kerby2000/PetSafe-PCB/output/measurement_round1-1.png

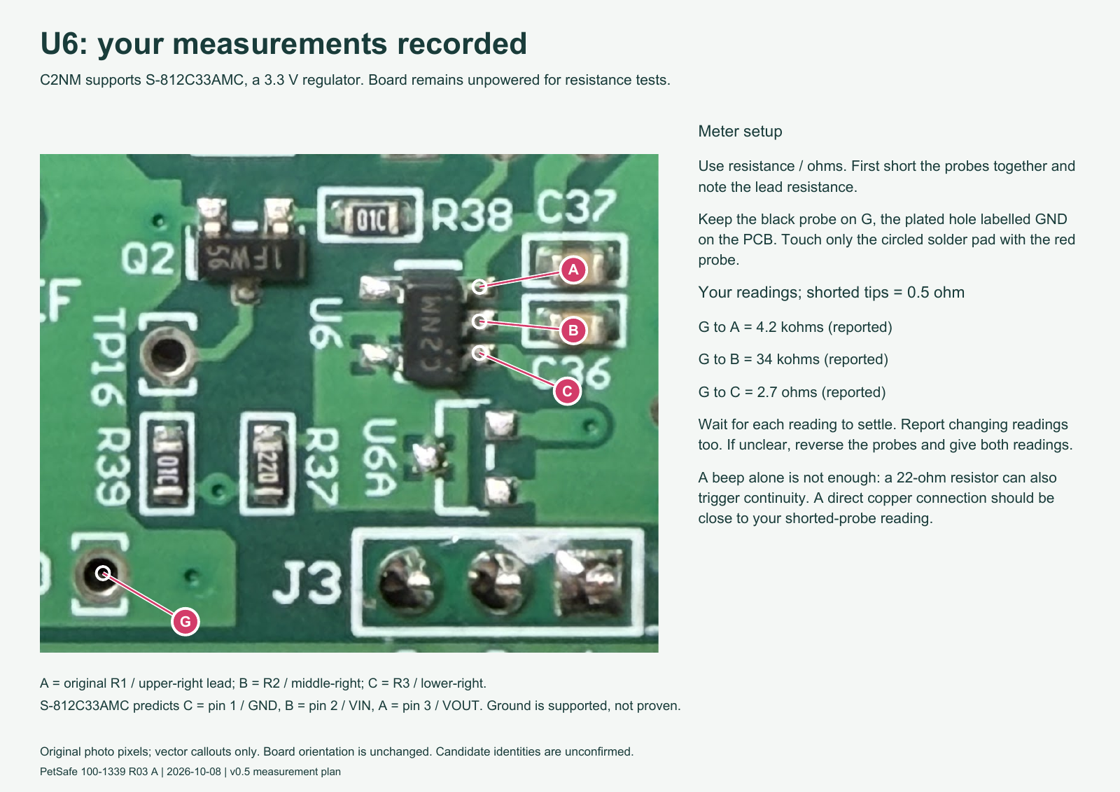
output/measurement_round1-1.png
