kerby2000/PetSafe-PCB/output/D2_D3_location_v1.png

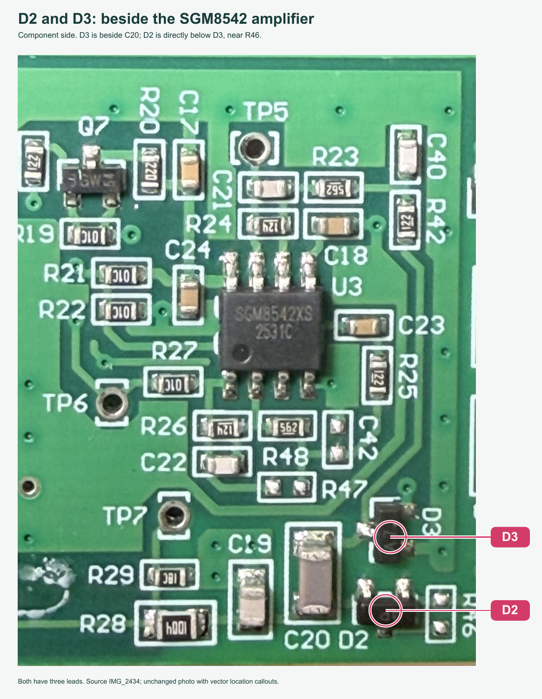
output/D2_D3_location_v1.png
