kerby2000/PetSafe-PCB/output/PetSafe_PIC_GPIO_pin_map.png

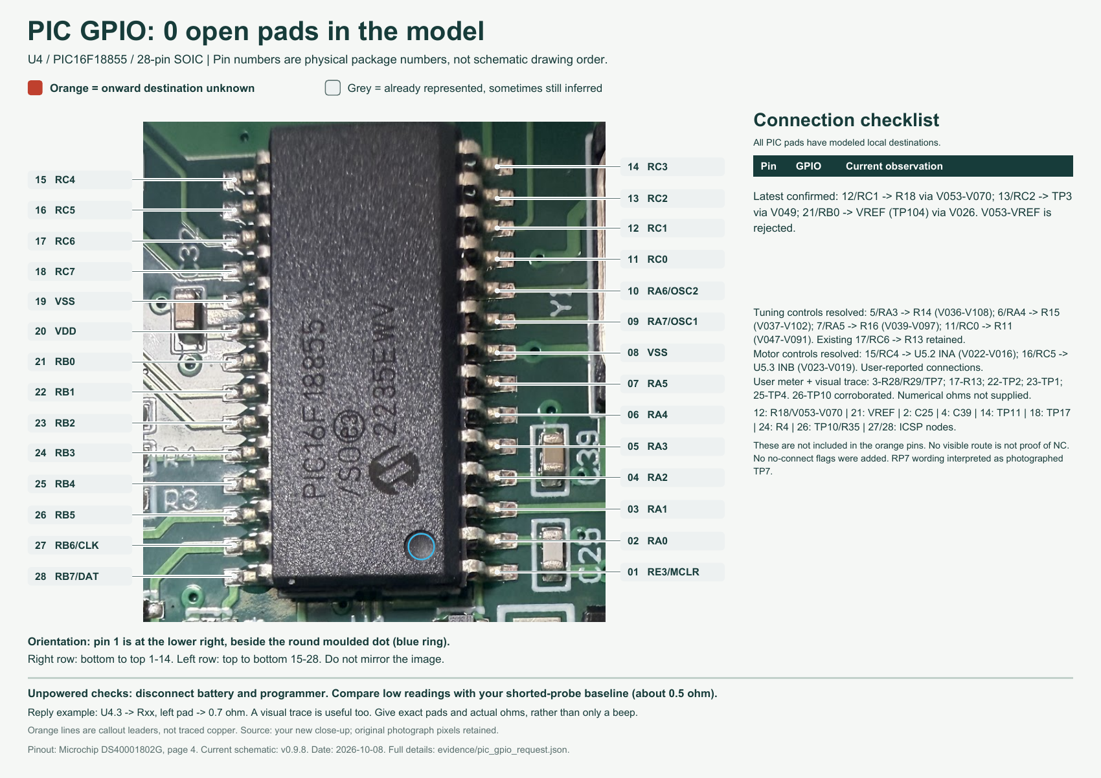
output/PetSafe_PIC_GPIO_pin_map.png
