kerby2000/PetSafe-PCB/output/Q8_C6_followup_with_P.png

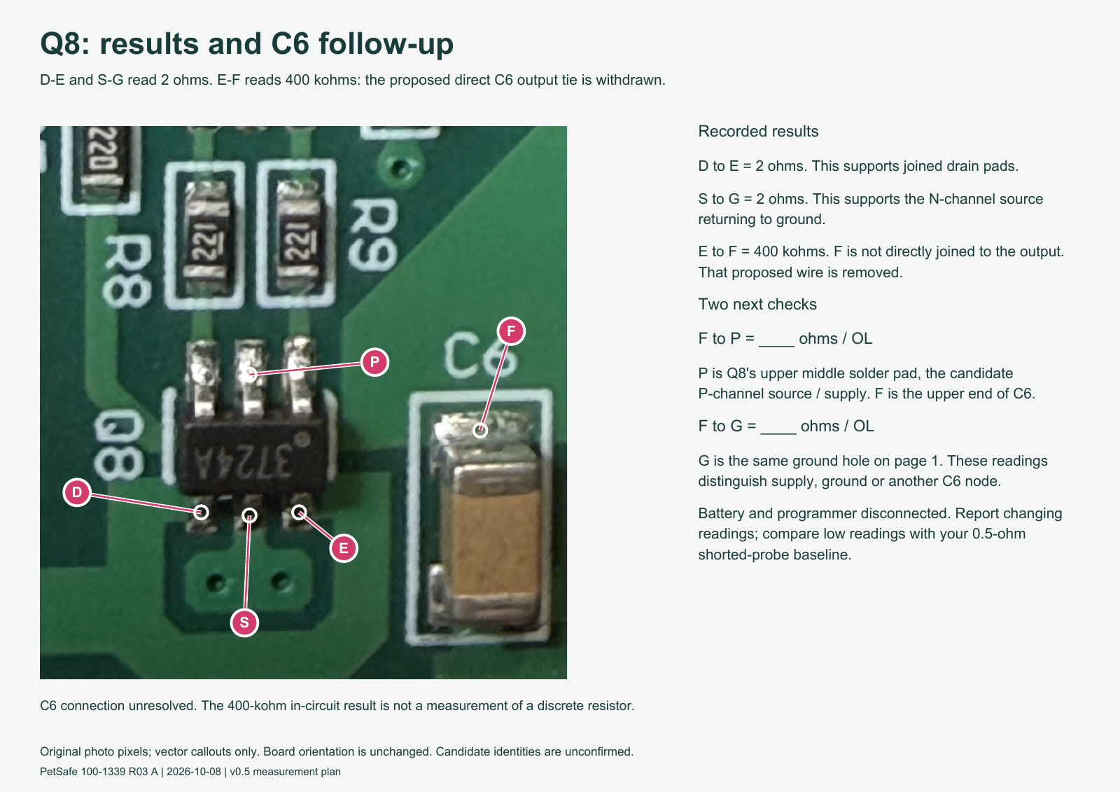
output/Q8_C6_followup_with_P.png
