kerby2000/PetSafe-PCB/output/single_sheet_preview.png

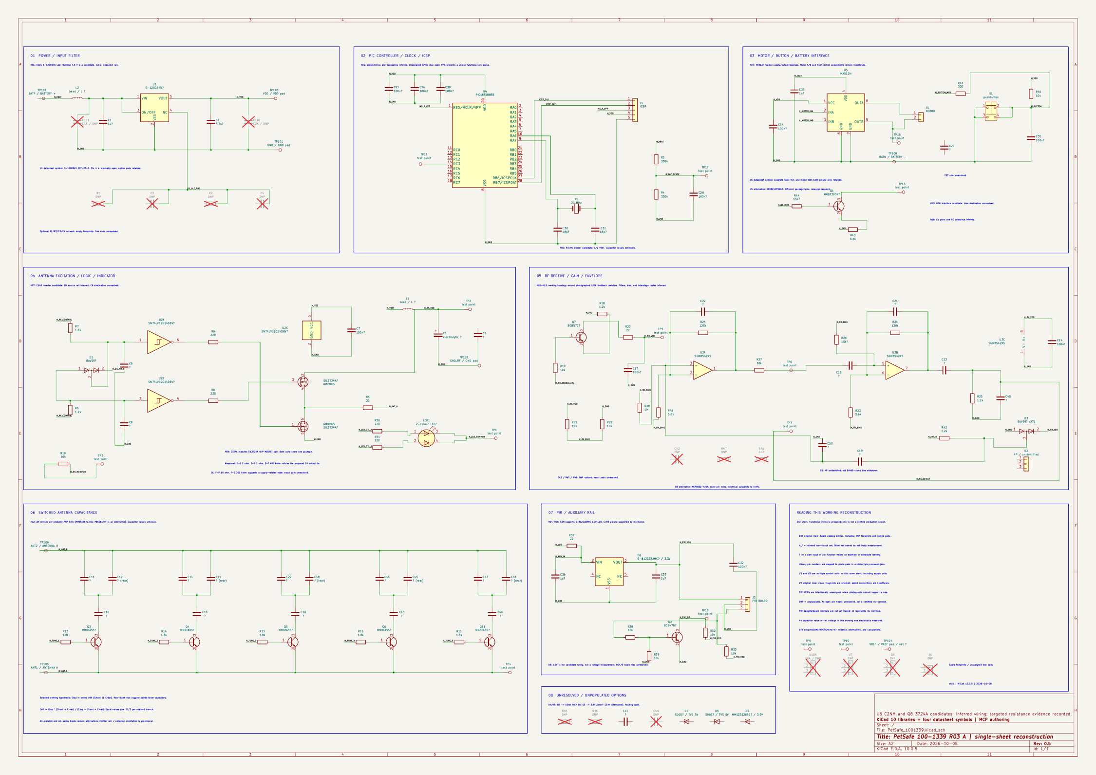
output/single_sheet_preview.png
