kerby2000/PetSafe-PCB/photos/back_mirrored_registered.jpg

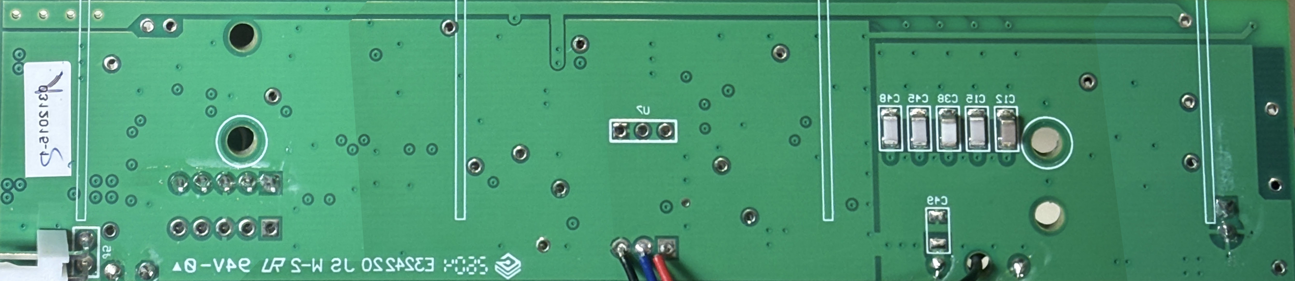
photos/back_mirrored_registered.jpg
