kerby2000/PetSafe-PCB/photos/back_readable.jpg

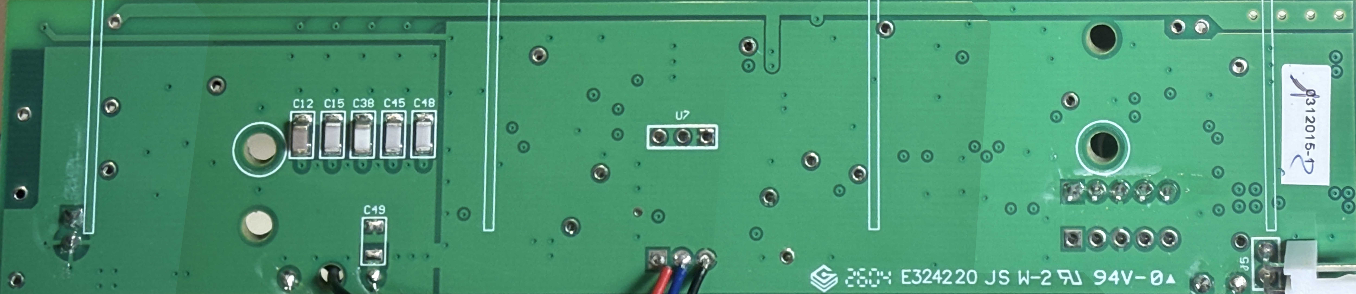
photos/back_readable.jpg
