kerby2000/PetSafe-PCB/photos/back_source_ids_unrectified.png

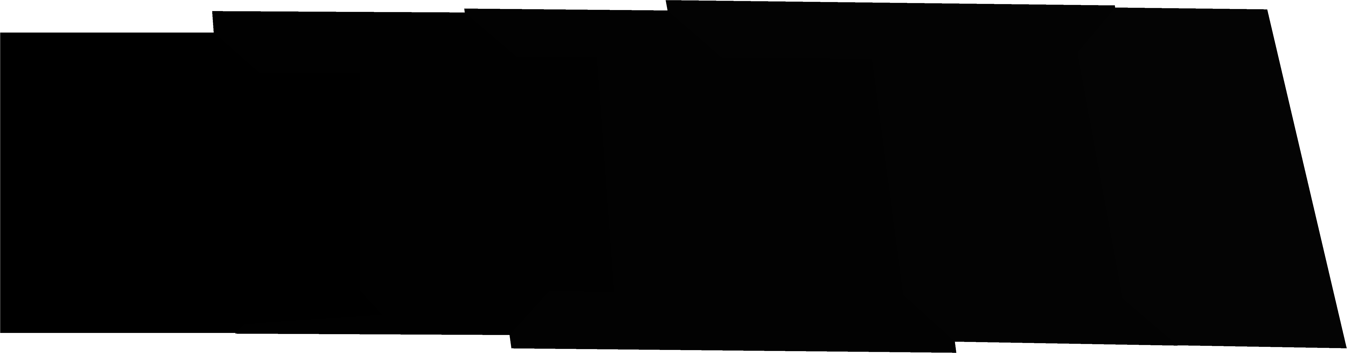
photos/back_source_ids_unrectified.png
