kerby2000/PetSafe-PCB/photos/front_preview.jpg

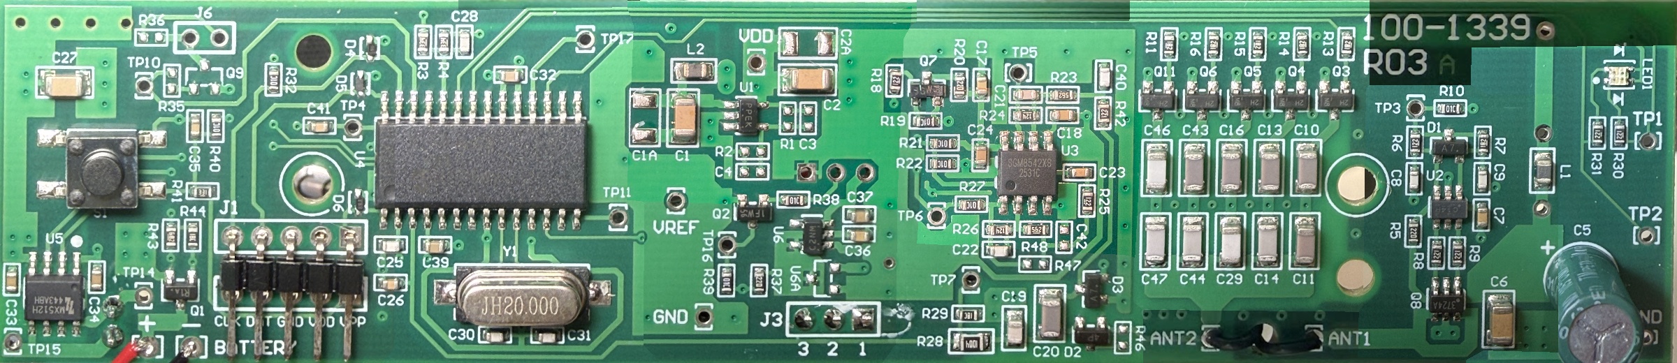
photos/front_preview.jpg
