kerby2000/PetSafe-PCB/photos/investigation/Q8_detail.png

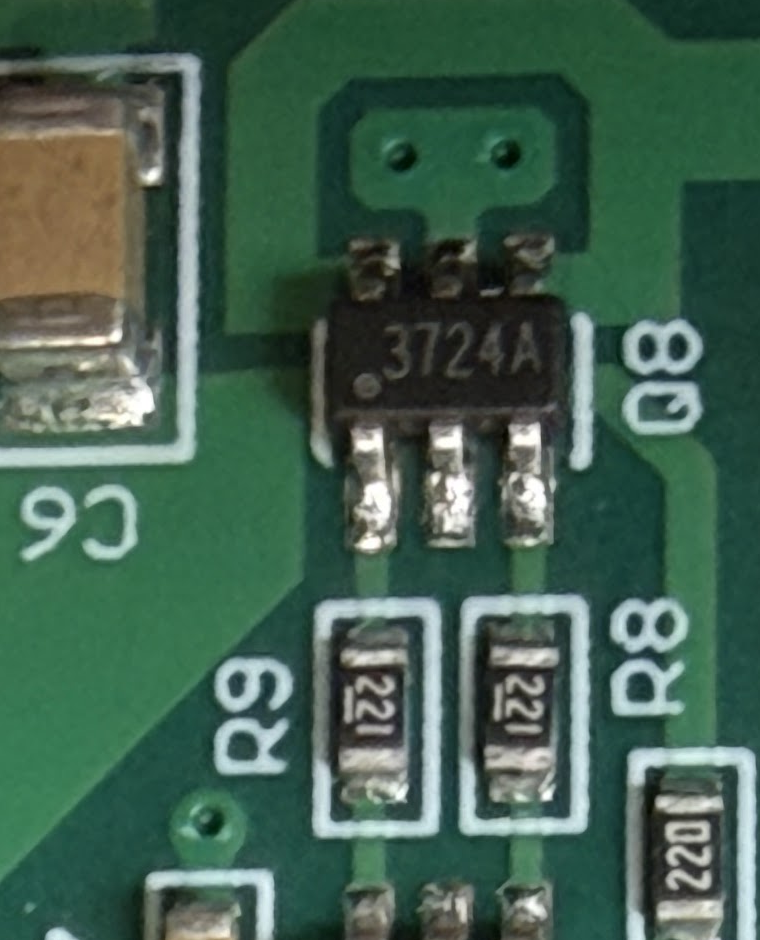
photos/investigation/Q8_detail.png
