kerby2000/PetSafe-PCB/photos/investigation/U6_detail.png

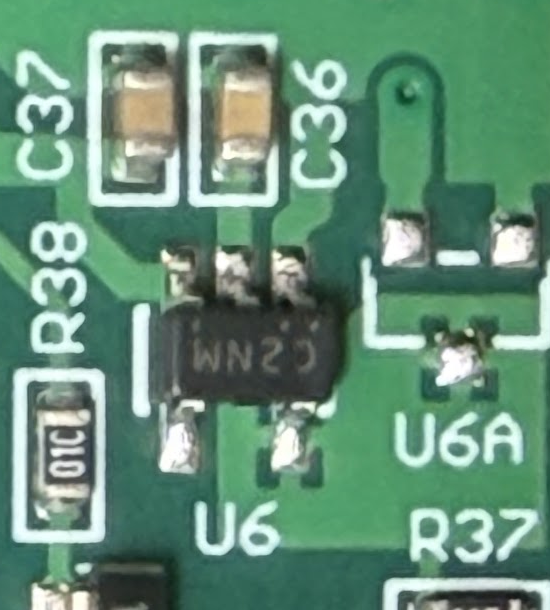
photos/investigation/U6_detail.png
