kerby2000/PetSafe-PCB/photos/originals/IMG_2417.jpg

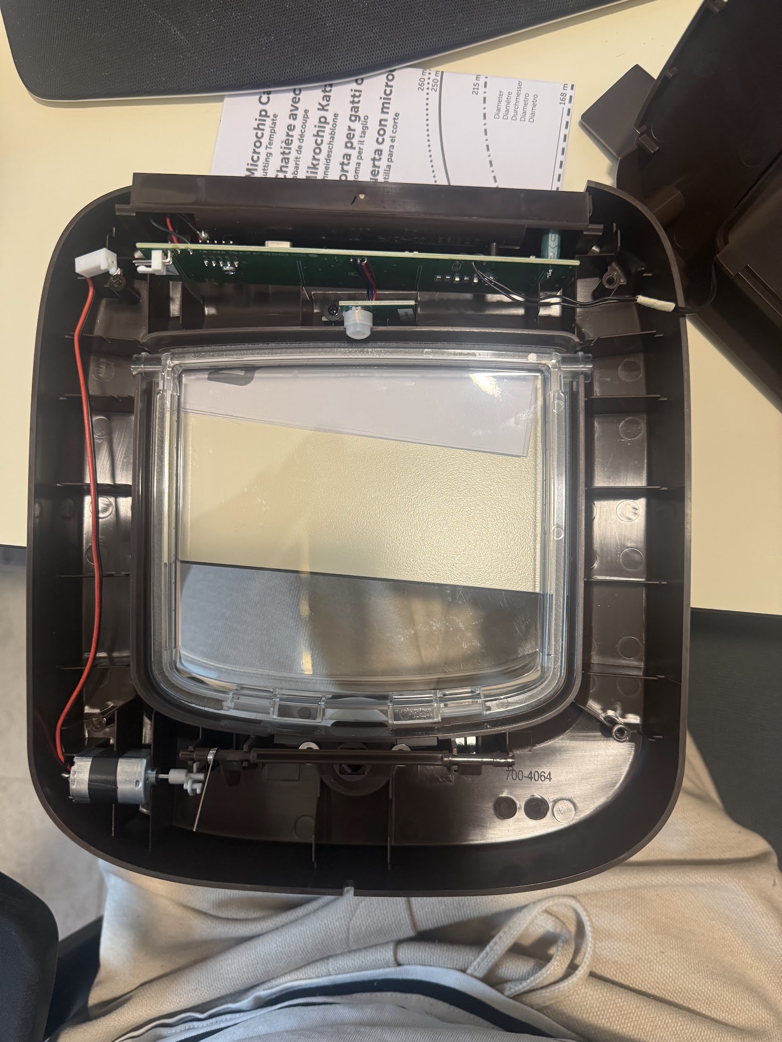
photos/originals/IMG_2417.jpg
