kerby2000/PetSafe-PCB/photos/originals/IMG_2418.jpg

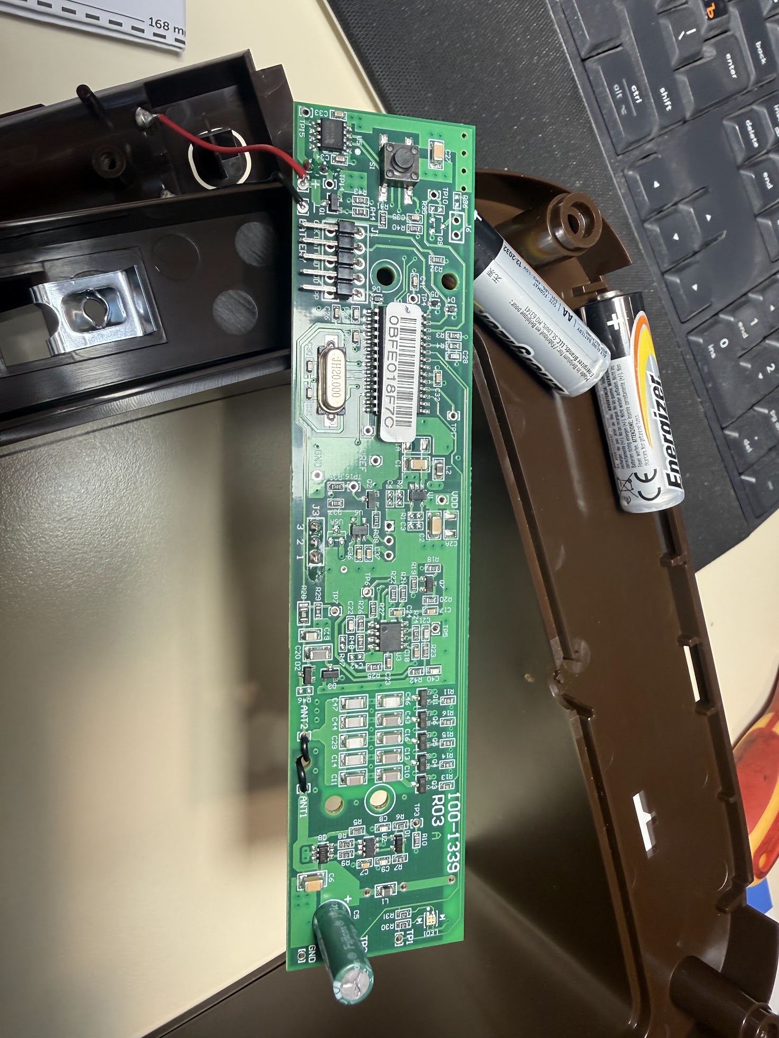
photos/originals/IMG_2418.jpg
