kerby2000/PetSafe-PCB/photos/originals/IMG_2419.jpg

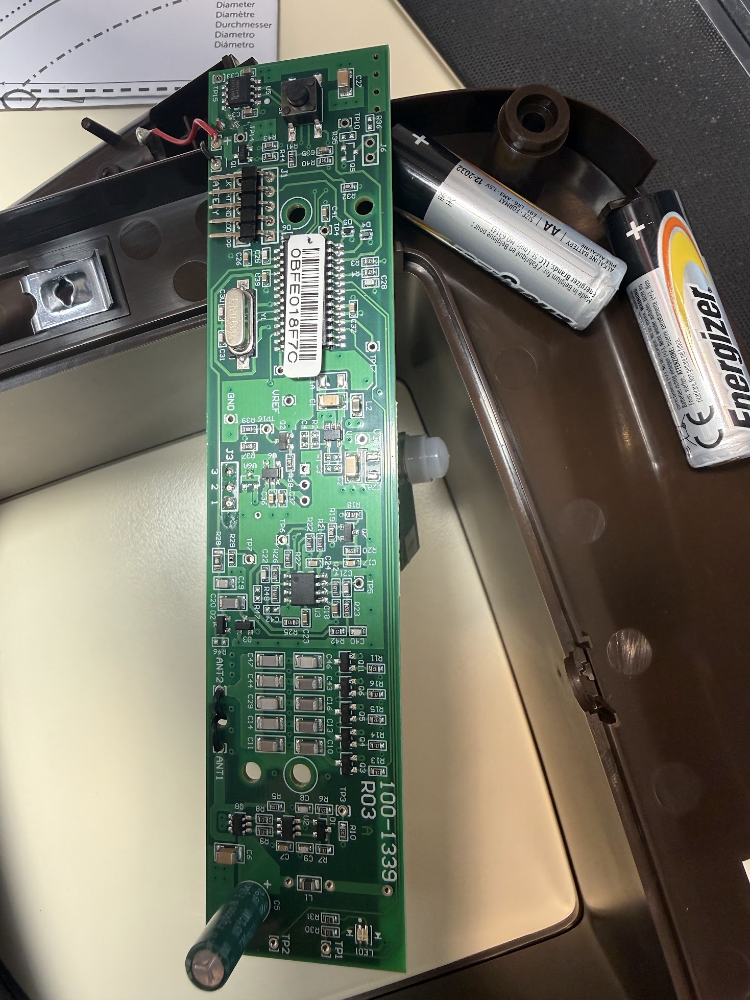
photos/originals/IMG_2419.jpg
