kerby2000/PetSafe-PCB/photos/originals/IMG_2420.jpg

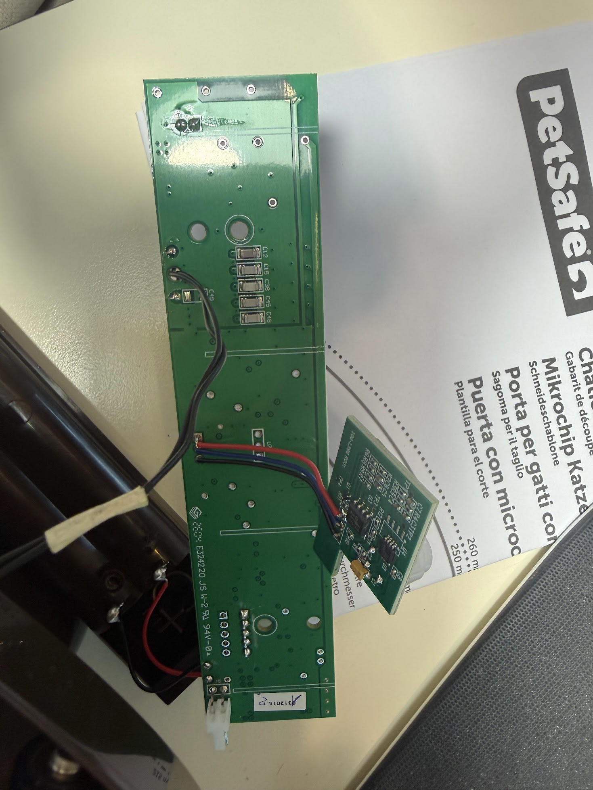
photos/originals/IMG_2420.jpg
