kerby2000/PetSafe-PCB/photos/originals/IMG_2421.jpg

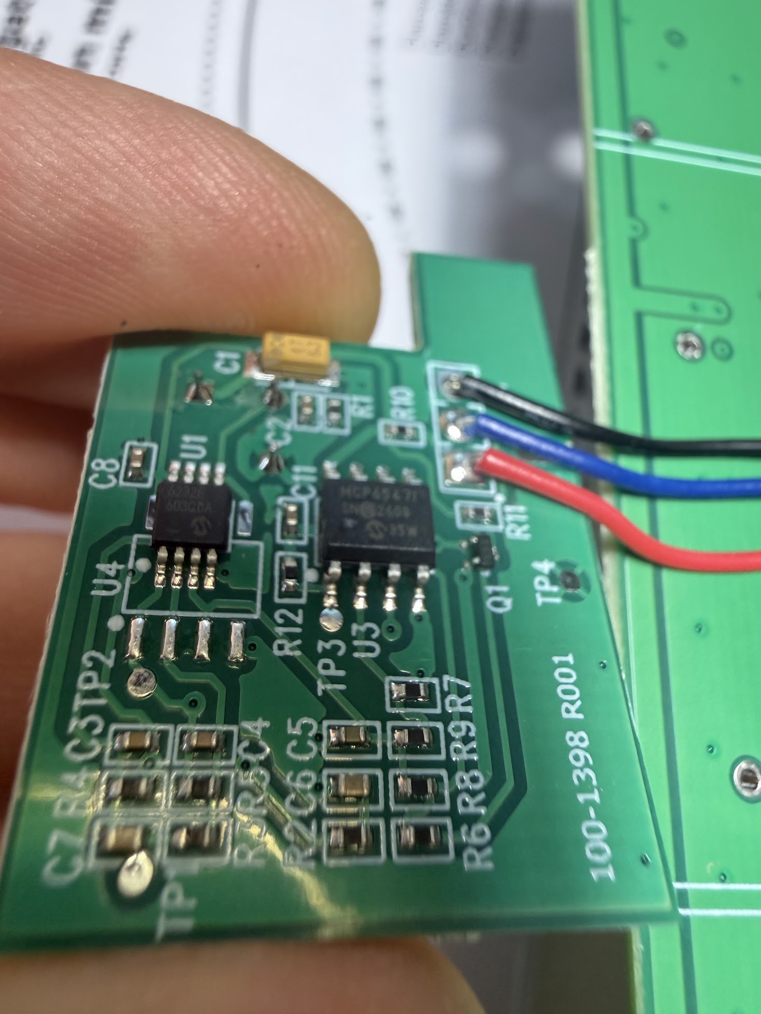
photos/originals/IMG_2421.jpg
