kerby2000/PetSafe-PCB/photos/originals/IMG_2422.jpg

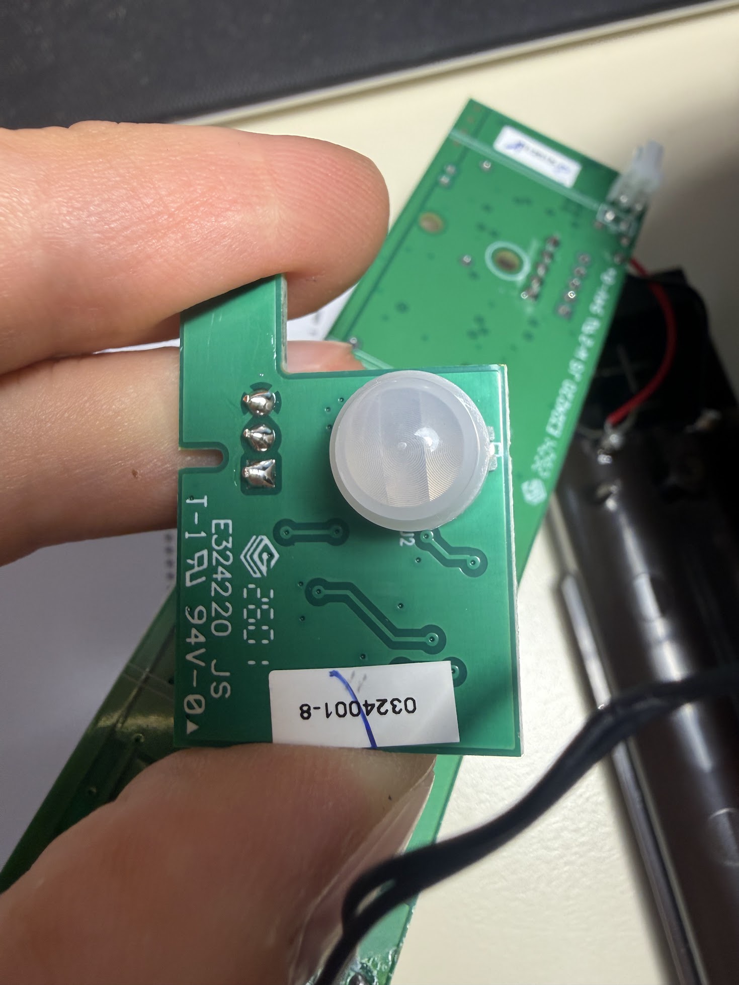
photos/originals/IMG_2422.jpg
