kerby2000/PetSafe-PCB/photos/originals/IMG_2423.jpg

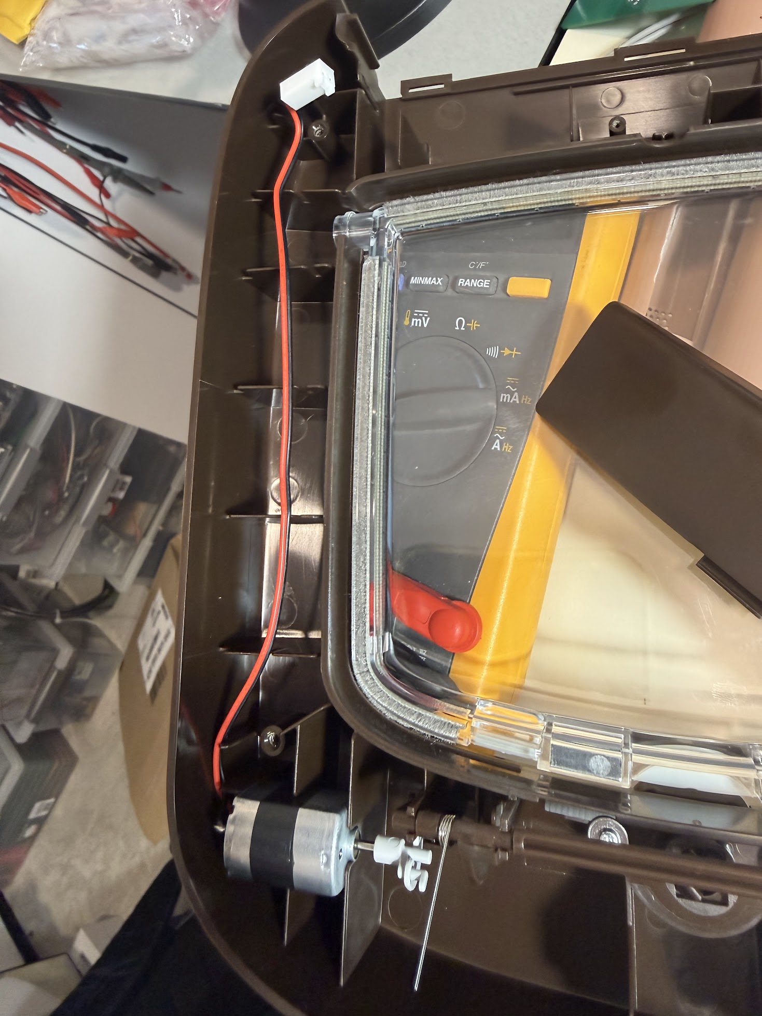
photos/originals/IMG_2423.jpg
