kerby2000/PetSafe-PCB/photos/originals/IMG_2424.jpg

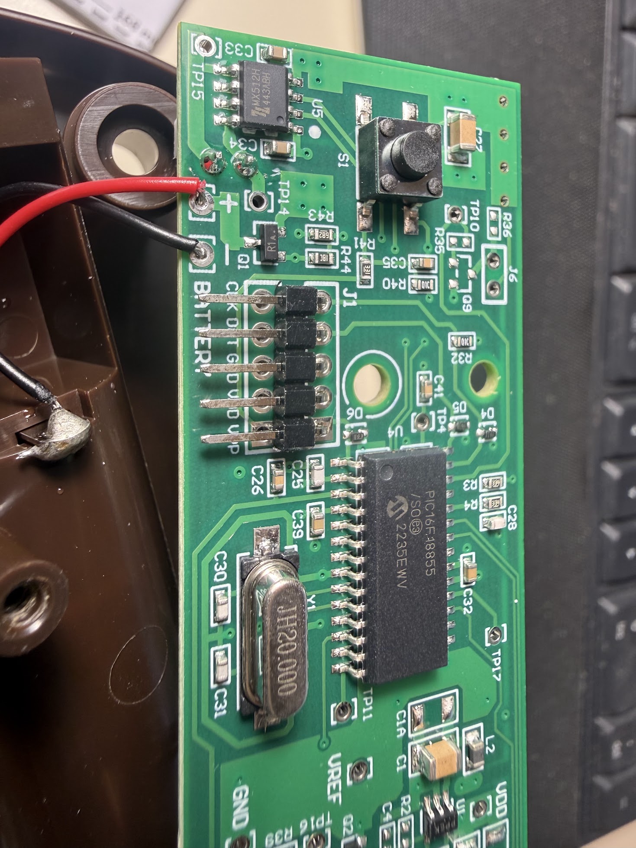
photos/originals/IMG_2424.jpg
