kerby2000/PetSafe-PCB/photos/originals/IMG_2425.jpg

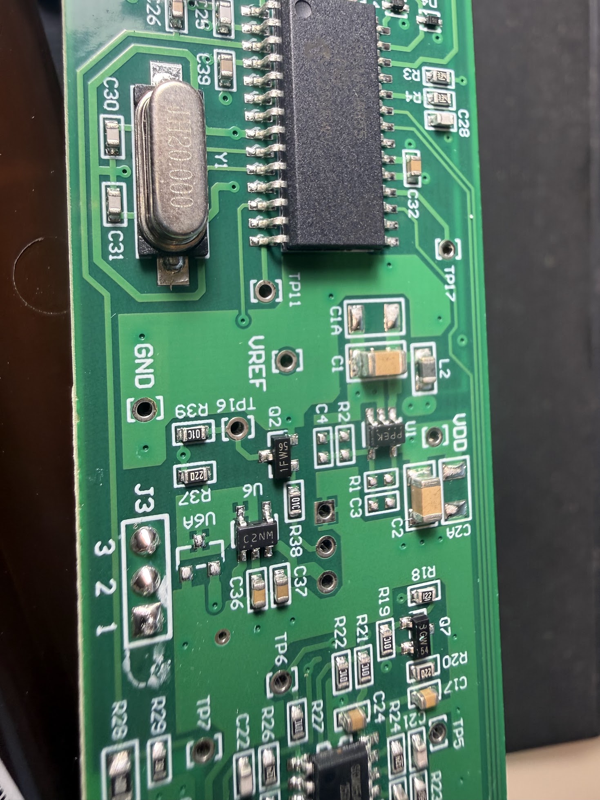
photos/originals/IMG_2425.jpg
