kerby2000/PetSafe-PCB/photos/originals/IMG_2427.jpg

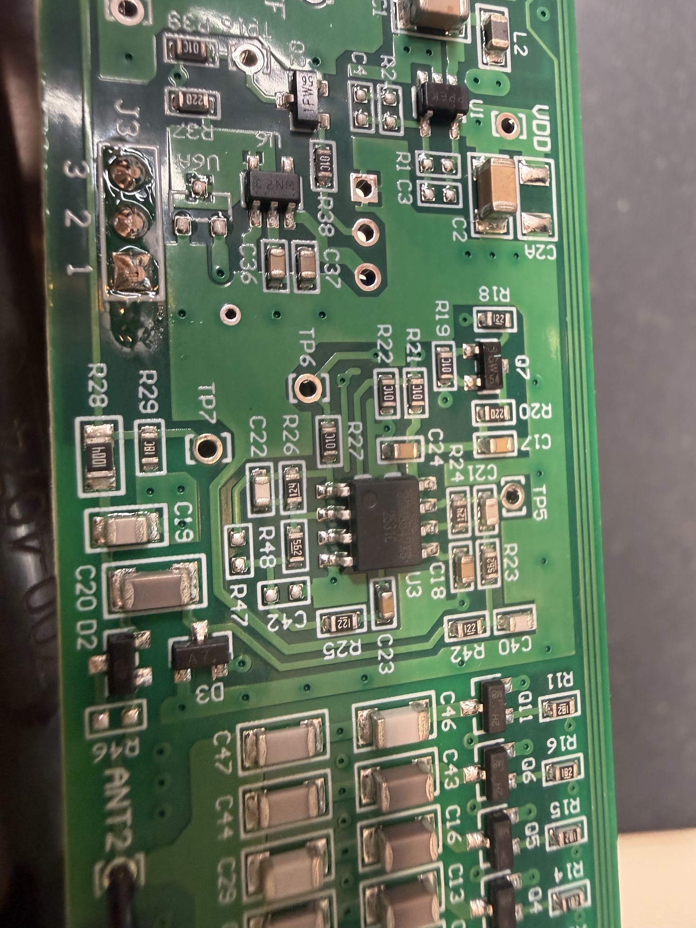
photos/originals/IMG_2427.jpg
