kerby2000/PetSafe-PCB/photos/originals/IMG_2428.jpg

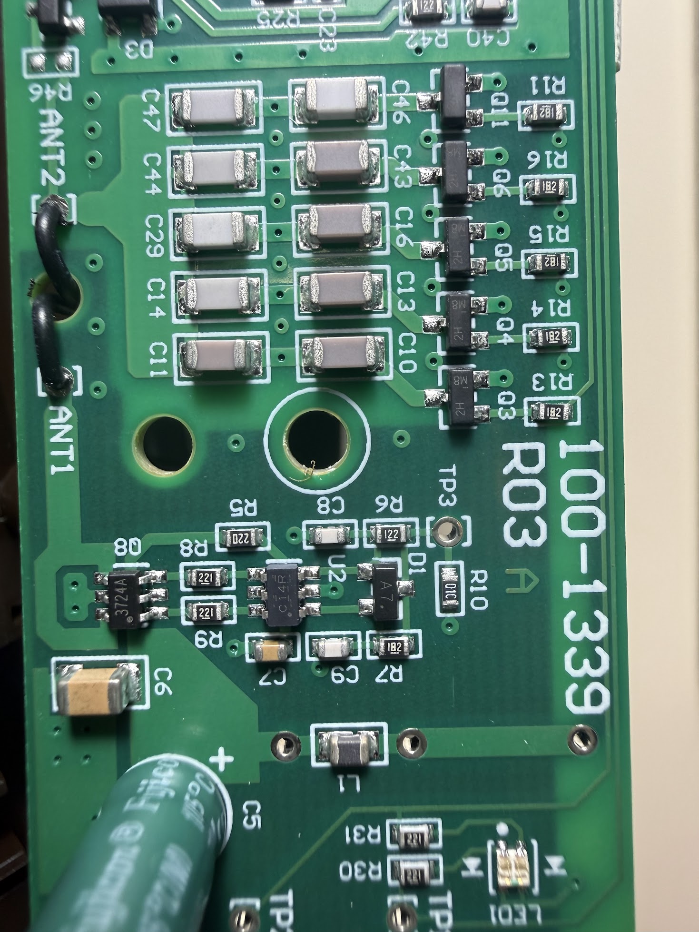
photos/originals/IMG_2428.jpg
