kerby2000/PetSafe-PCB/photos/originals/IMG_2429.jpg

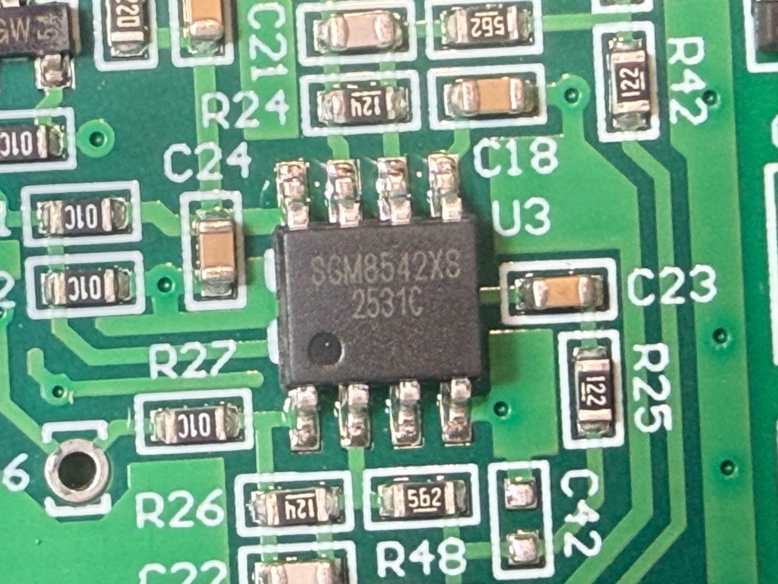
photos/originals/IMG_2429.jpg
