kerby2000/PetSafe-PCB/photos/originals/IMG_2430.jpg

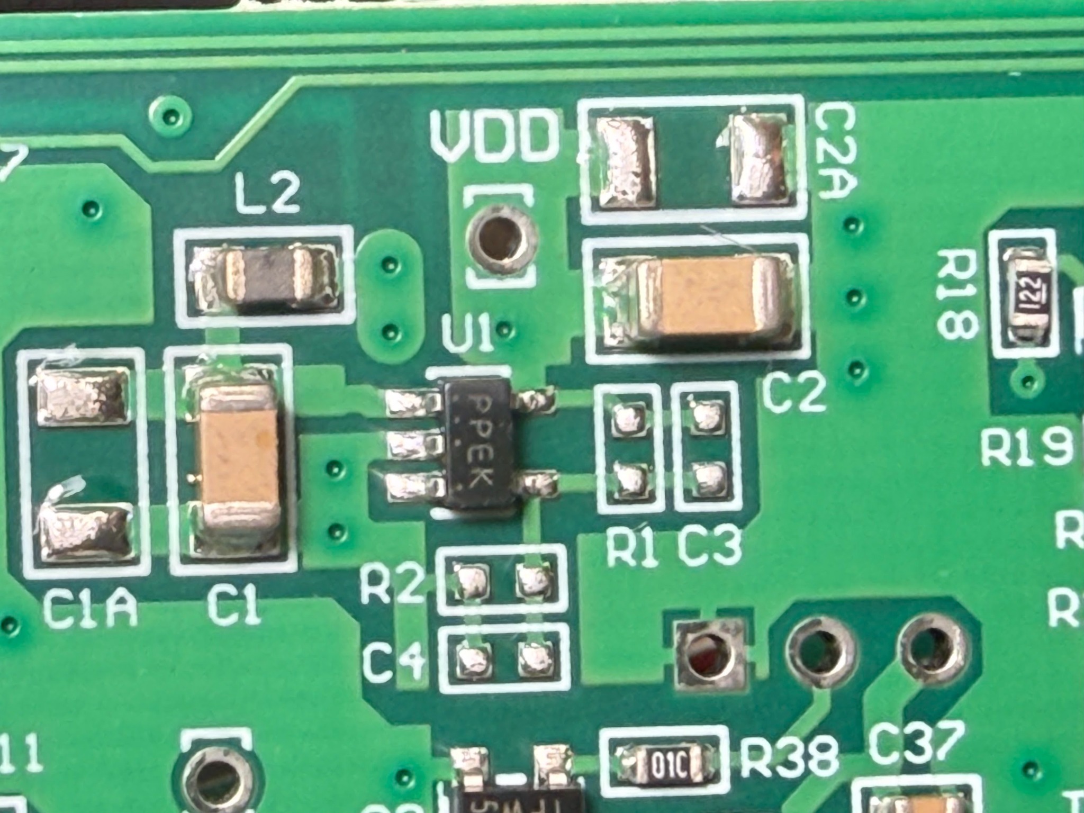
photos/originals/IMG_2430.jpg
