kerby2000/PetSafe-PCB/photos/originals/IMG_2431.jpg

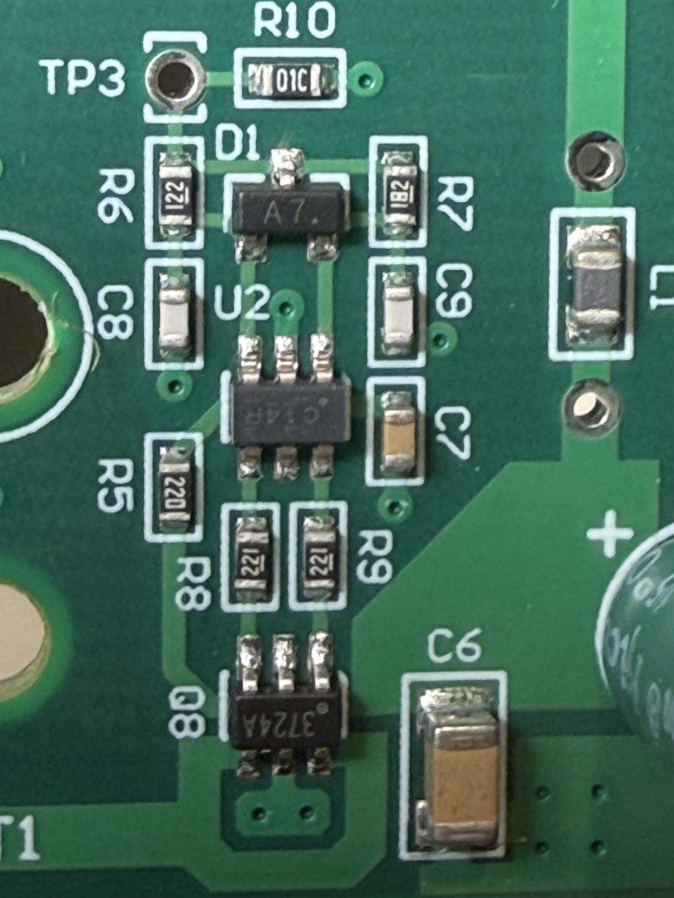
photos/originals/IMG_2431.jpg
