kerby2000/PetSafe-PCB/photos/originals/IMG_2432.jpg

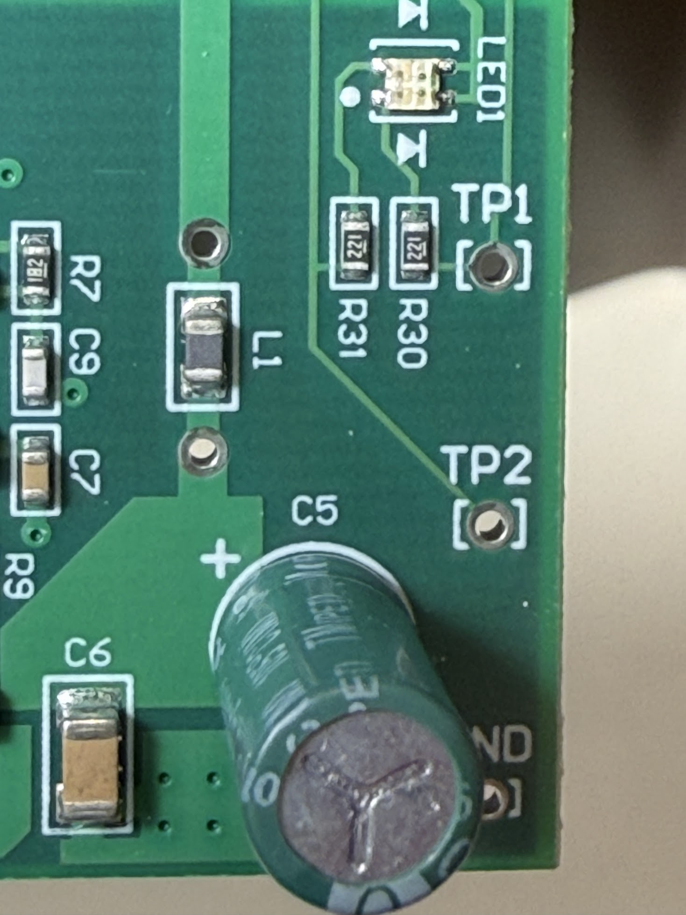
photos/originals/IMG_2432.jpg
