kerby2000/PetSafe-PCB/photos/originals/IMG_2433.jpg

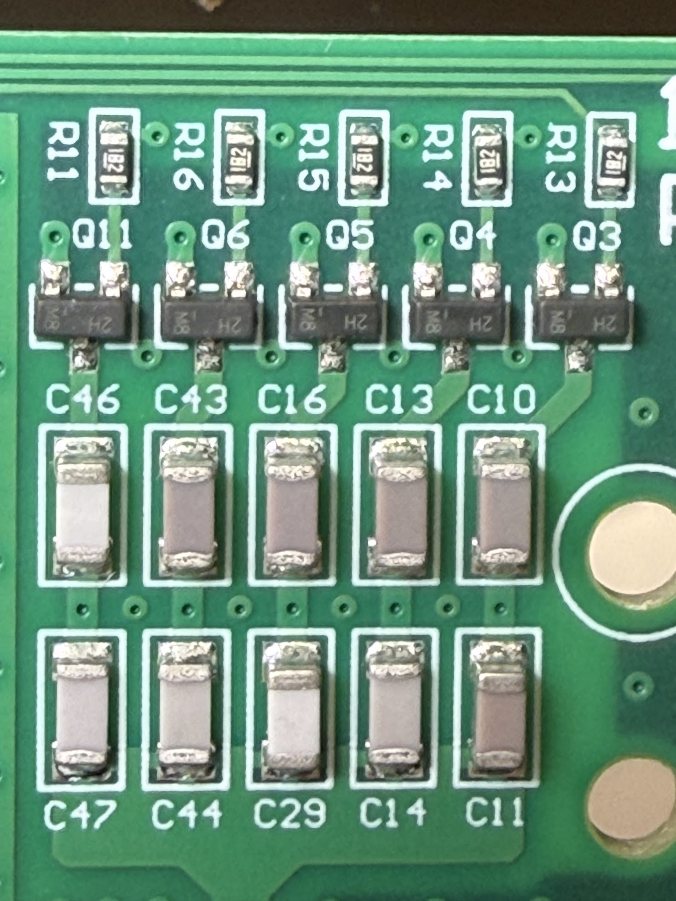
photos/originals/IMG_2433.jpg
