kerby2000/PetSafe-PCB/photos/originals/IMG_2434.jpg

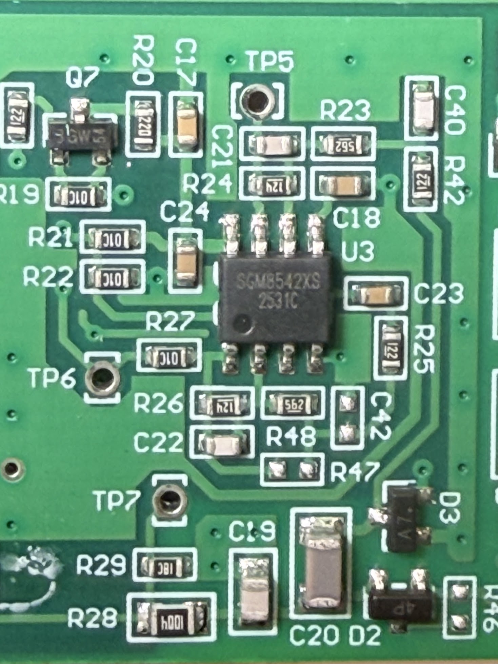
photos/originals/IMG_2434.jpg
