kerby2000/PetSafe-PCB/photos/originals/IMG_2435.jpg

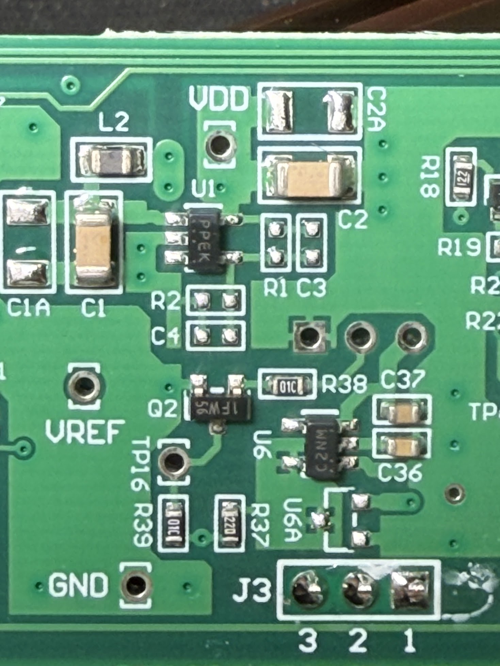
photos/originals/IMG_2435.jpg
