kerby2000/PetSafe-PCB/photos/originals/IMG_2436.jpg

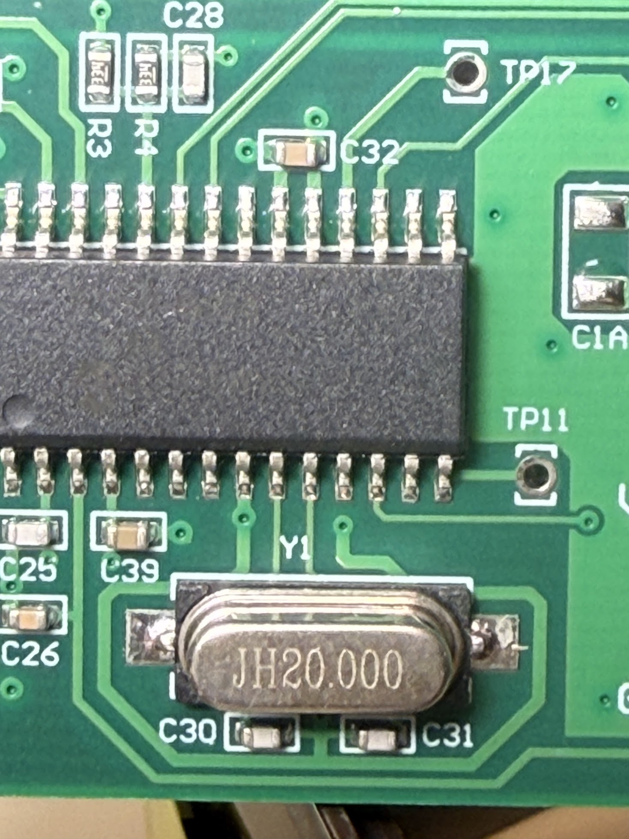
photos/originals/IMG_2436.jpg
