kerby2000/PetSafe-PCB/photos/originals/IMG_2437.jpg

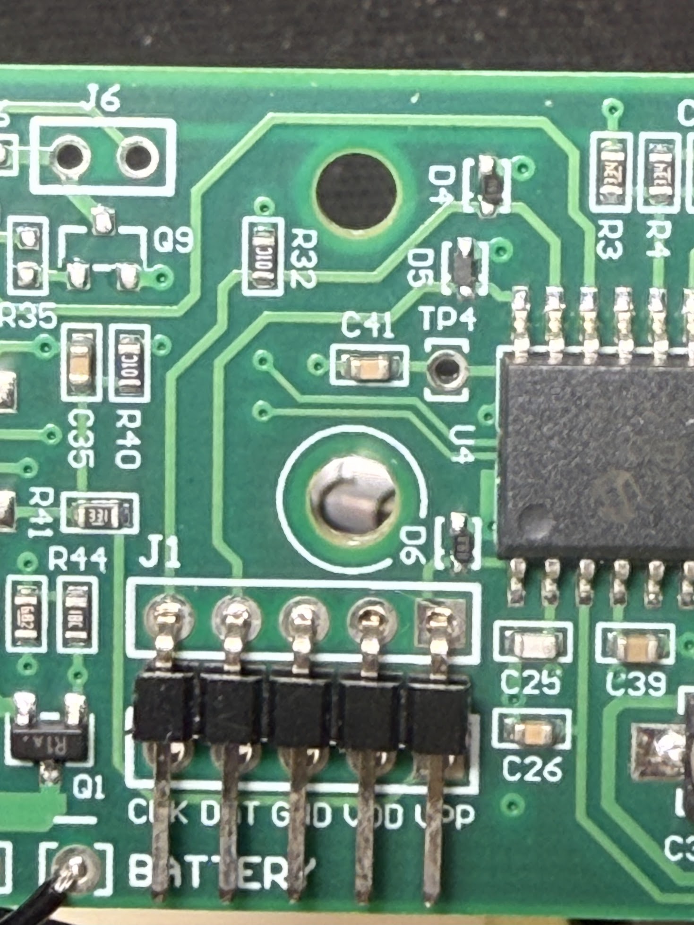
photos/originals/IMG_2437.jpg
