kerby2000/PetSafe-PCB/photos/originals/IMG_2438.jpg

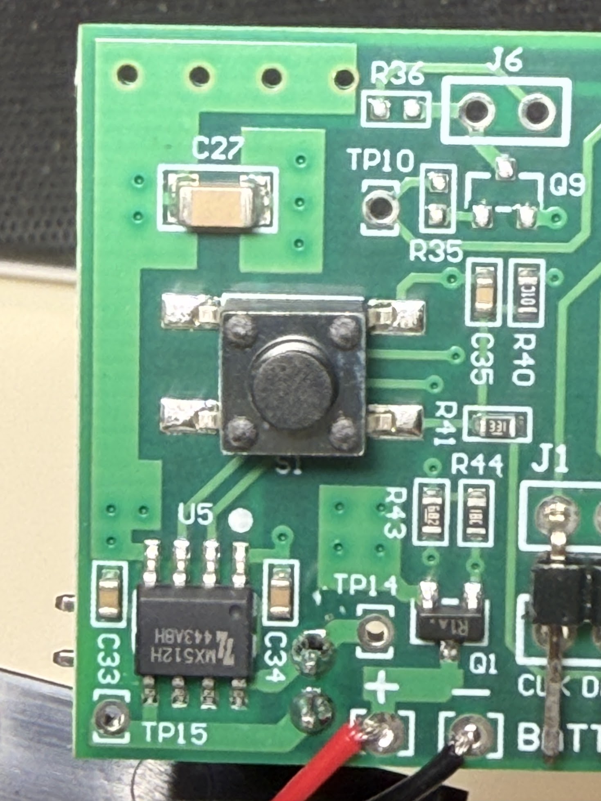
photos/originals/IMG_2438.jpg
