kerby2000/PetSafe-PCB/photos/originals/IMG_2439.jpg

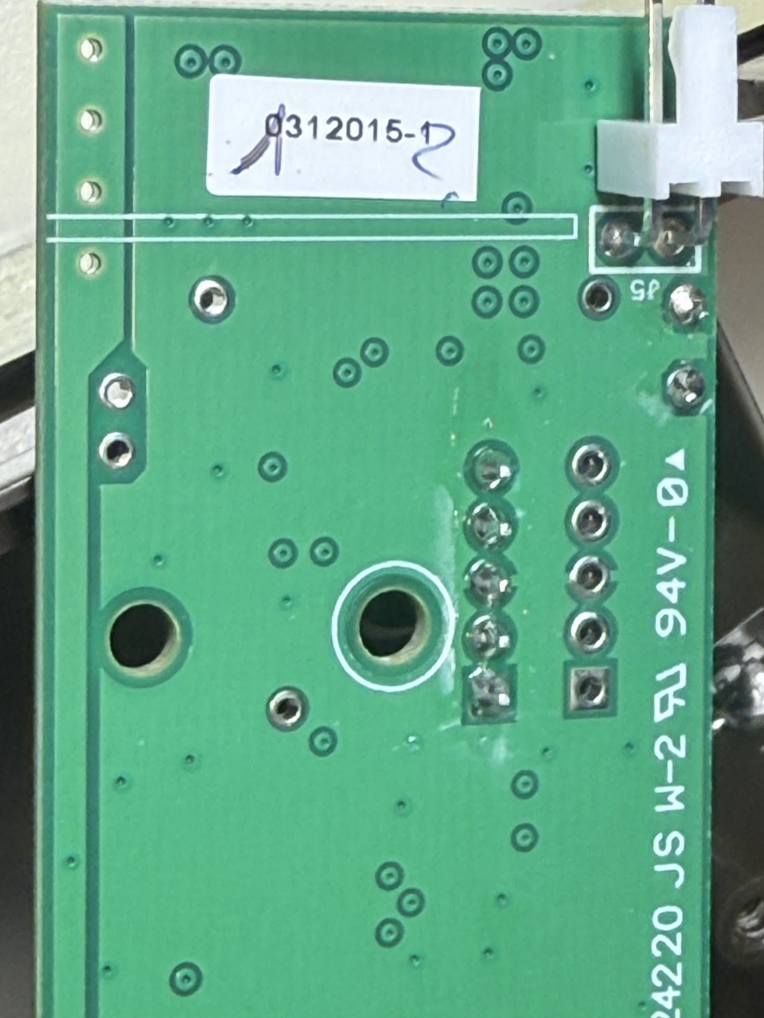
photos/originals/IMG_2439.jpg
