kerby2000/PetSafe-PCB/photos/originals/IMG_2440.jpg

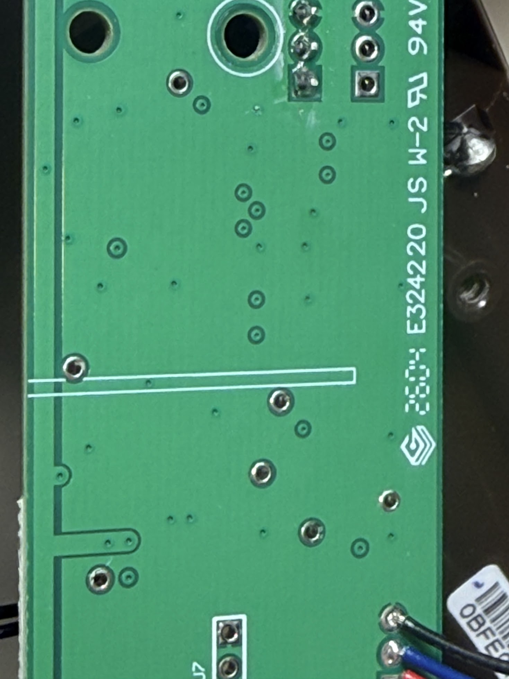
photos/originals/IMG_2440.jpg
