kerby2000/PetSafe-PCB/photos/originals/IMG_2441.jpg

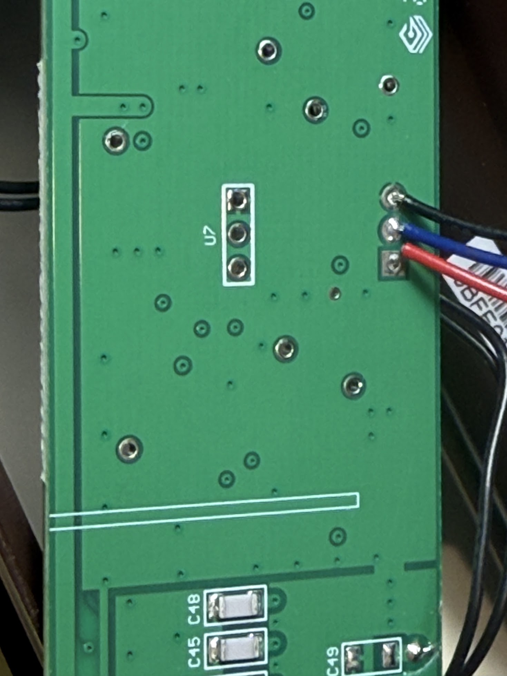
photos/originals/IMG_2441.jpg
