kerby2000/PetSafe-PCB/photos/originals/IMG_2442.jpg

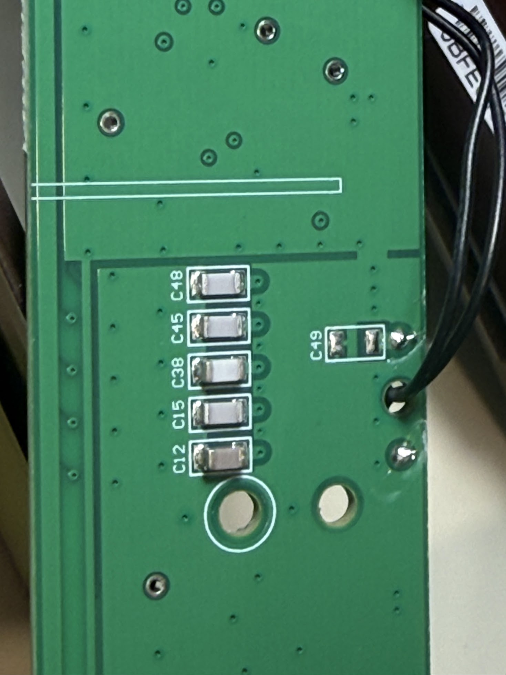
photos/originals/IMG_2442.jpg
