kerby2000/PetSafe-PCB/photos/originals/IMG_2443.jpg

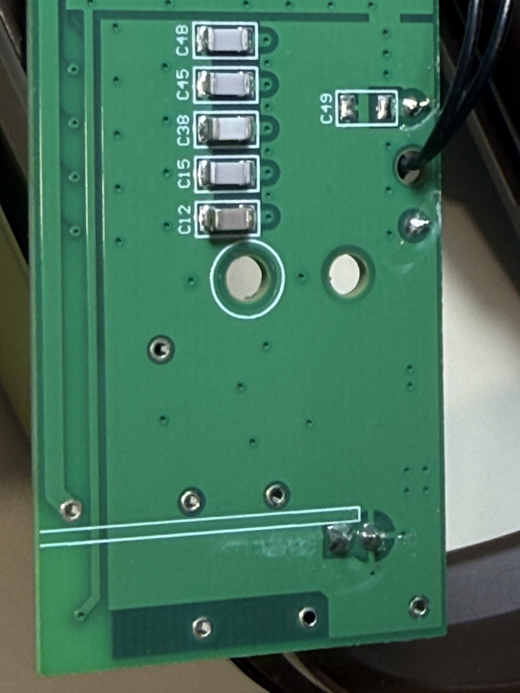
photos/originals/IMG_2443.jpg
