kerby2000/PetSafe-PCB/photos/U4_probe_orientation.png

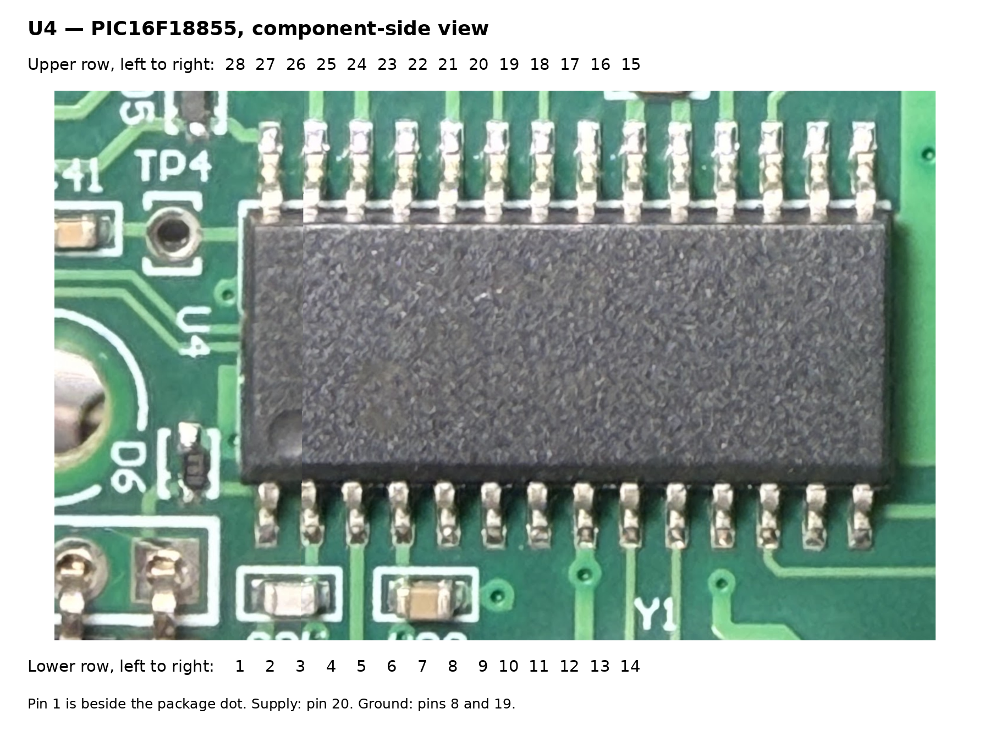
photos/U4_probe_orientation.png
