kerby2000/PetSafe-PCB/photos/U5_probe_orientation.png

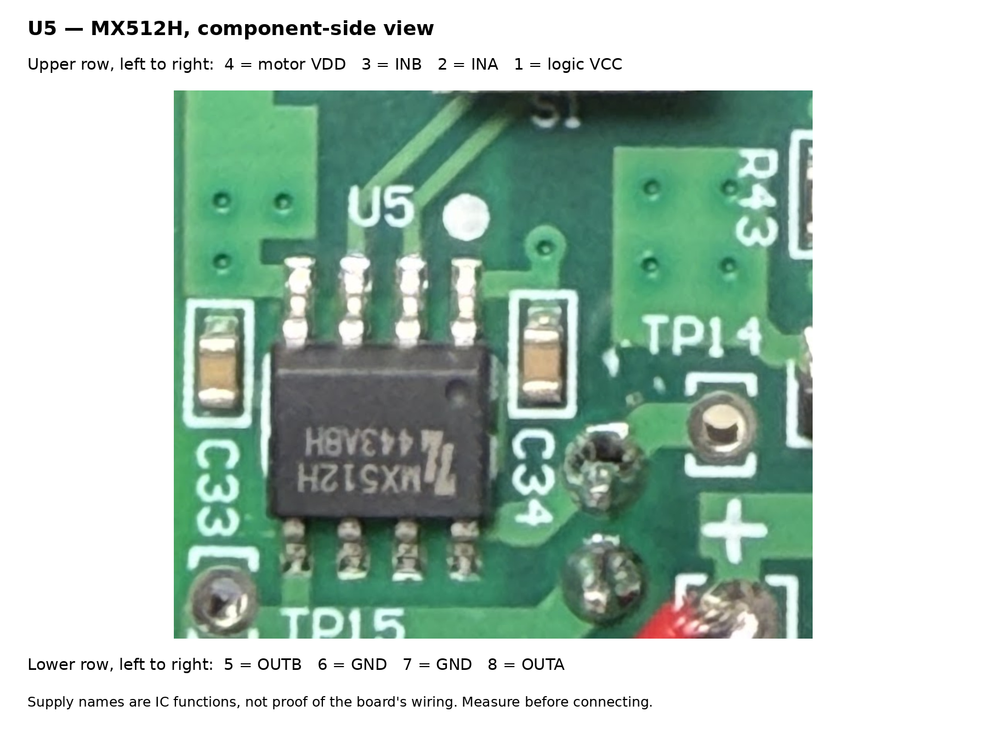
photos/U5_probe_orientation.png
