kerby2000/PetSafe-PCB/photos/user/2026-10-08/board_full.png

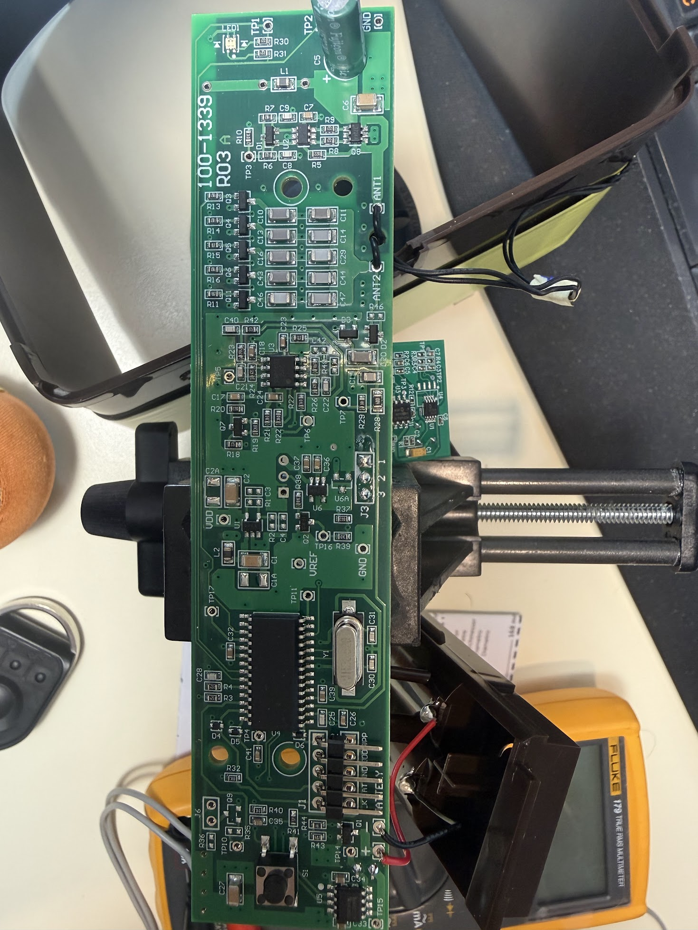
photos/user/2026-10-08/board_full.png
