kerby2000/PetSafe-PCB/photos/user/2026-10-08/board_upper.png

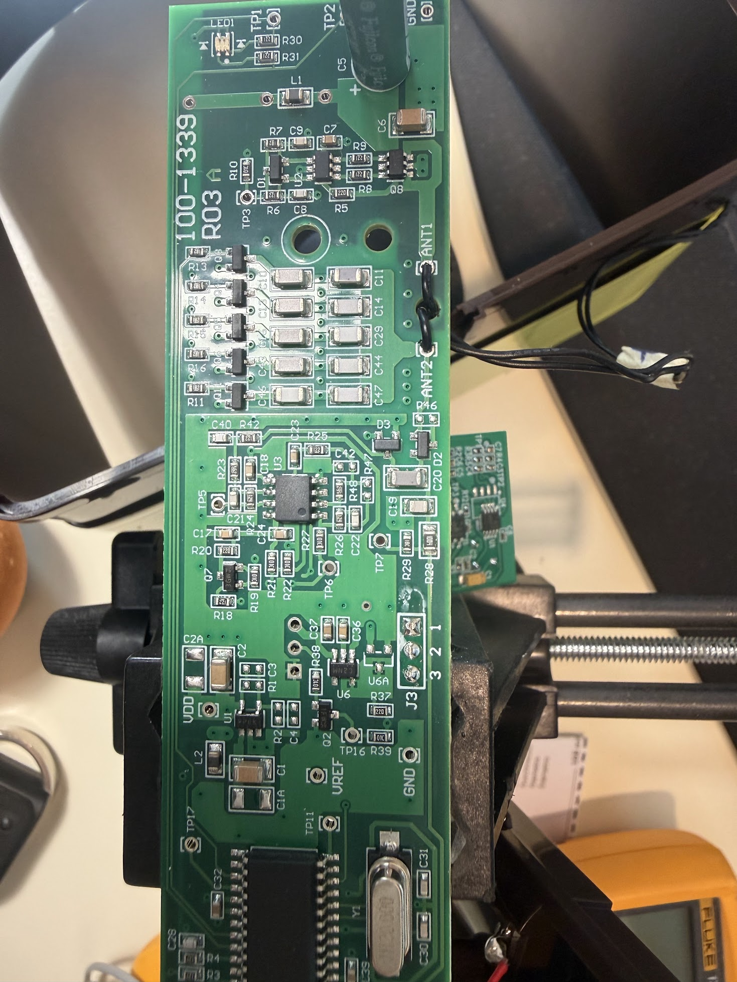
photos/user/2026-10-08/board_upper.png
