kerby2000/PetSafe-PCB/photos/user/2026-10-08/pic_closeup.png

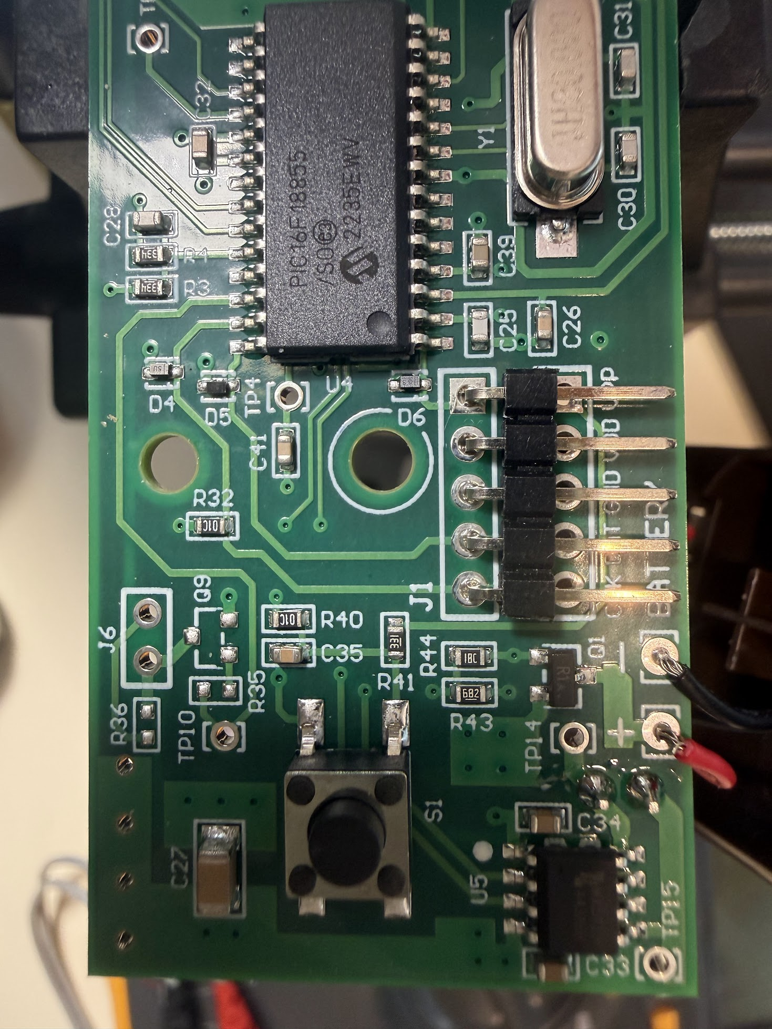
photos/user/2026-10-08/pic_closeup.png
