kerby2000/PetSafe-PCB/photos/user/2026-10-08/VDD_user_locator.png

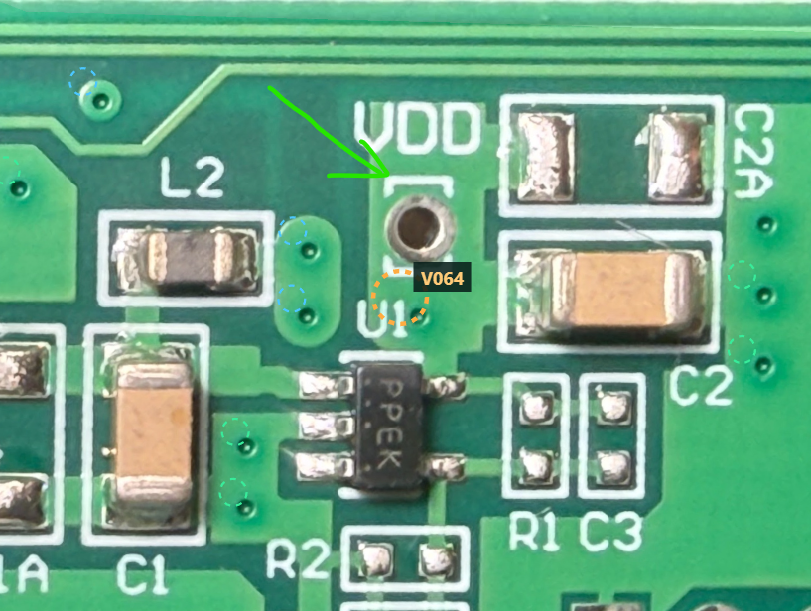
photos/user/2026-10-08/VDD_user_locator.png
