kerby2000/PetSafe-PCB/photos/user/2026-10-08/VREF_user_locator.png

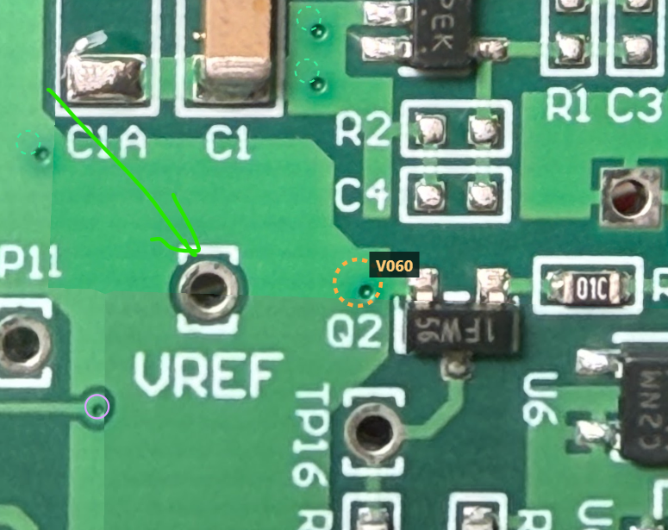
photos/user/2026-10-08/VREF_user_locator.png
