kerby2000/PetSafe-PCB/photos/user/Q1_battery_path_20261008.png

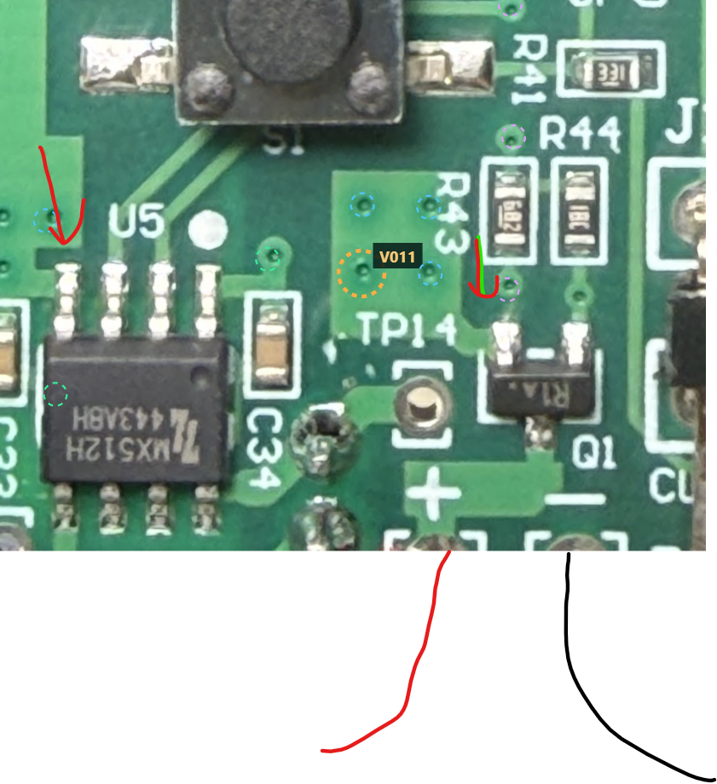
photos/user/Q1_battery_path_20261008.png
