kerby2000/PetSafe-PCB/photos/user/via_review/MX512H_pin4_supply.png

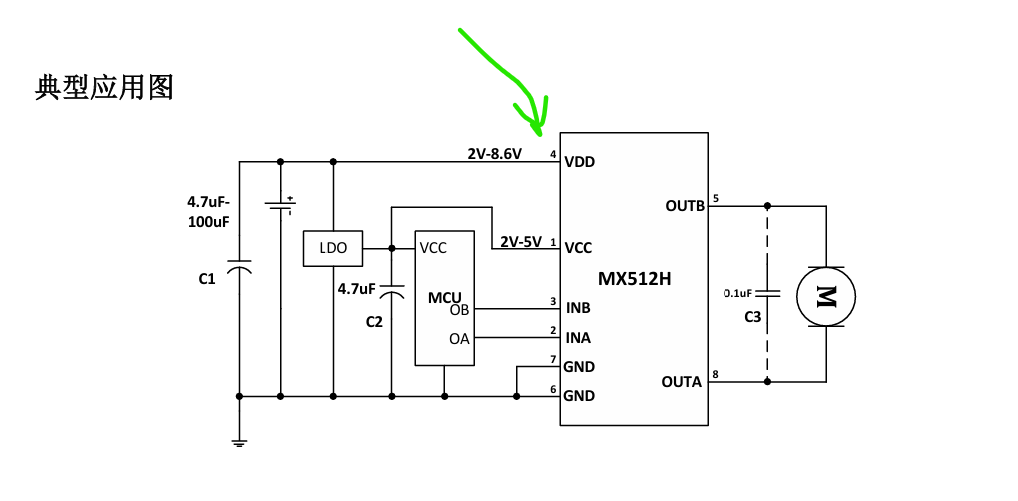
photos/user/via_review/MX512H_pin4_supply.png
