kerby2000/PetSafe-PCB/photos/user_updates/D4_5U.png

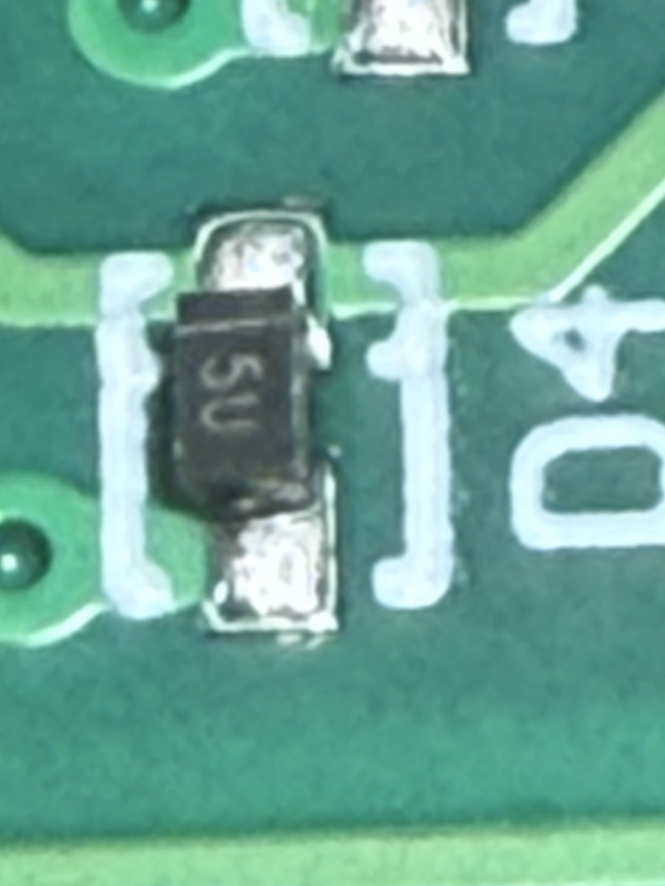
photos/user_updates/D4_5U.png
