kerby2000/PetSafe-PCB/photos/user_updates/D6_G3.png

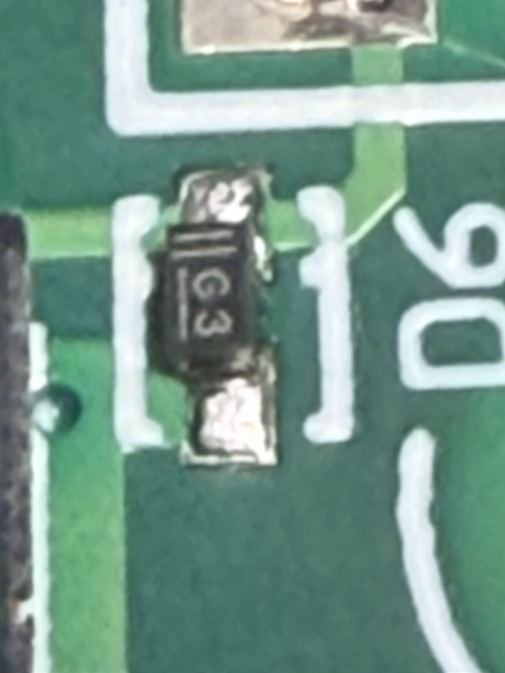
photos/user_updates/D6_G3.png
