kerby2000/PetSafe-PCB/photos/user_updates/U6_new_mark.png

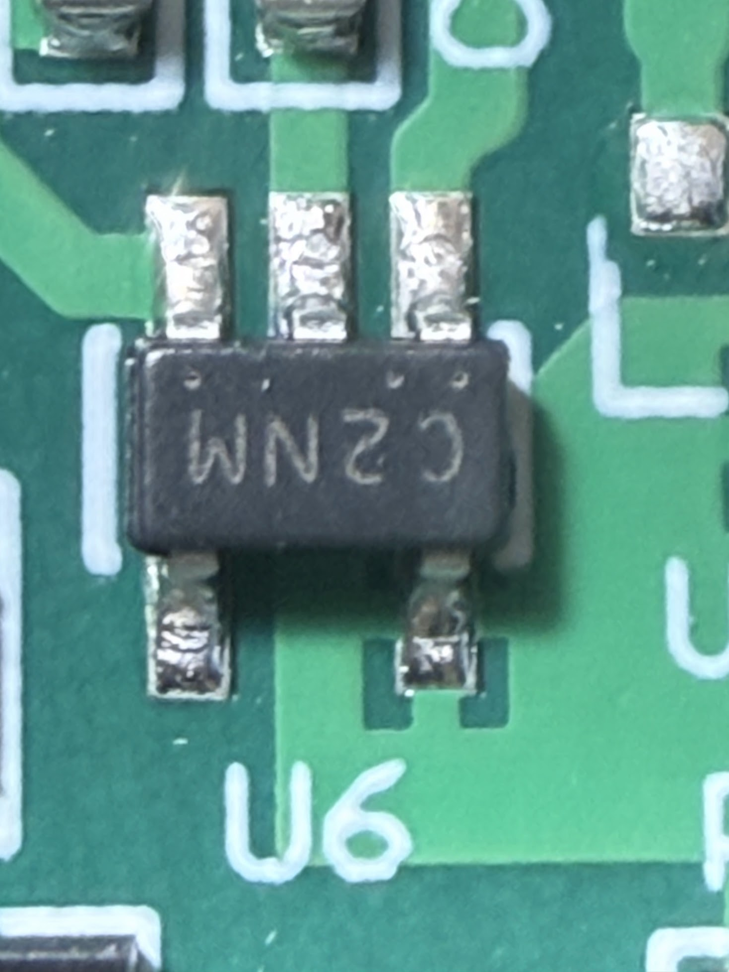
photos/user_updates/U6_new_mark.png
