kerby2000/PetSafe-PCB/schematic/PetSafe_1001339.kicad_sch

## KiCad design schematic/PetSafe_1001339.kicad_sch (2026-10-08)

Schematic: PetSafe_1001339.kicad_sch

Parts:
C1: 1u?; C_1206_3216Metric
C2: 4.7u?; C_1206_3216Metric
C3, C4, C42: DNP; C_0603_1608Metric; not fitted
C5: 470uF / 16V; Voltage 16V
C6, C10, C11, C13, C14, C16, C20, C27, C29, C43, C44, C46, C47: ?; C_1206_3216Metric
C7, C17, C24, C28, C32, C34, C35: 100n?; C_0805_2012Metric
C8, C9, C18, C19, C21, C22, C23, C25, C26, C39, C40, C41: ?; C_0805_2012Metric
C12, C15, C38, C45, C48: ? (rear); C_1206_3216Metric
C30, C31: 18p?; C_0805_2012Metric
C33, C36, C37: 1u?; C_0805_2012Metric
C49: DNP; C_1206_3216Metric; not fitted
C101: C1A / DNP; C_1206_3216Metric; not fitted
C102: C2A / DNP; C_1206_3216Metric; not fitted
D1: BAV99?; SOT-23
D2: 4P / unidentified; SOT-23
D3: BAV99? (A7); SOT-23
D4, D5: SD05? / TVS 5V; D_SOD-323
D6: MMSZ5228BS? / 3.9V; D_SOD-323
J1: ICSP; PinHeader_1x05_P2.54mm_Horizontal
J3: PIR BOARD; PinHeader_1x03_P2.54mm_Vertical
J5: MOTOR; JST_XH_B2B-XH-A_1x02_P2.50mm_Vertical
J6: DNP; PinHeader_1x02_P2.54mm_Vertical; not fitted
L1, L2: bead / L ?; L_0805_2012Metric
LED1: 2-colour LED?
Q1: FMOS3401A?; SOT-23
Q2: BC847B?; SOT-23
Q3, Q4, Q5, Q6, Q11: MMBTA55?; SOT-23
Q7: BC857C?; SOT-23
Q8: SIL3724A?; SOT-23-6
Q9: DNP; SOT-23; not fitted
R1, R2, R35, R36, R46, R47: DNP; R_0603_1608Metric; not fitted
R3, R4: 330k; R_0603_1608Metric
R5, R20, R37: 22; R_0603_1608Metric
R6, R18, R25, R42: 1.2k; R_0603_1608Metric
R7, R11, R13, R14, R15, R16: 1.8k; R_0603_1608Metric
R8, R9, R30, R31: 220; R_0603_1608Metric
R10, R19, R21, R22, R27, R32, R33, R38, R39, R40: 10k; R_0603_1608Metric
R23, R48: 5.6k; R_0603_1608Metric
R24, R26: 120k; R_0603_1608Metric
R28: 1M; R_0603_1608Metric
R29, R44: 15k; R_0603_1608Metric
R41: 330; R_0603_1608Metric
R43: 6.8k; R_0603_1608Metric
S1: pushbutton
TP1, TP2, TP3, TP4, TP5, TP6, TP7, TP9, TP10, TP11, TP14, TP15, TP16, TP17: test point; TestPoint_THTPad_D2.0mm_Drill1.0mm
TP101: GND; TestPoint_THTPad_D2.0mm_Drill1.0mm
TP102: GND_RF / GND pad; TestPoint_THTPad_D2.0mm_Drill1.0mm
TP103: VDD; TestPoint_THTPad_D2.0mm_Drill1.0mm
TP104: VREF; TestPoint_THTPad_D2.0mm_Drill1.0mm
TP105: ANT1 / ANTENNA A; TestPoint_THTPad_D2.0mm_Drill1.0mm
TP106: ANT2 / ANTENNA B; TestPoint_THTPad_D2.0mm_Drill1.0mm
TP107: BATTERY (+); TestPoint_THTPad_2.5x2.5mm_Drill1.2mm
TP108: BATTERY (-); TestPoint_THTPad_2.5x2.5mm_Drill1.2mm
U1: S-1200B45?; SOT-23-5
U2: SN74LVC2G14DBV?; SOT-23-6
U3: SGM8542XS; SOIC-8_3.9x4.9mm_P1.27mm
U4: PIC16F18855; SOIC-28W_7.5x17.9mm_P1.27mm
U5: MX512H; SOIC-8_3.9x4.9mm_P1.27mm
U6: S-812C33AMC? / 3.3V; SOT-23-5
U7: DNP; PinHeader_1x03_P2.54mm_Vertical; not fitted
U106: U6A / DNP; SOT-23; not fitted
Y1: 20 MHz; Crystal_SMD_HC49-SD

Connections:
BATTERY+: Q1.3 (D), R43.2, TP14.1, TP107.1
GND: C1.2, C2.2, C4.1, C5.2, C6.2, C7.2, C8.2, C9.2, C11.1, C12.1, C14.1, C15.1, C17.2, C19.2, C20.1, C24.2, C25.2, C26.2, C27.2, C28.2, C29.1, C30.2, C31.1, C32.2, C33.2, C34.2, C35.2, C36.2, C37.2, C38.1, C39.2, C40.2, C41.2, C44.1, C45.1, C47.1, C48.1, C101.2, C102.2, D3.1 (K), D4.2 (A), D5.2 (A), J1.5, J3.2, LED1.3 (K1), LED1.4 (K2), Q2.2 (E), Q3.2 (E), Q4.2 (E), Q5.2 (E), Q6.2 (E), Q8.5 (S), Q9.2, Q11.2 (E), R2.1, R10.2, R22.1, R25.2, R29.2, R32.1, R43.1, S1.1, S1.3, TP101.1, TP102.1, TP108.1, U1.2 (VSS), U2.2 (GND), U3.4 (V-), U4.8 (VSS), U4.19 (VSS), U5.6 (GND), U5.7 (GND), U6.1 (VSS)
H_ANT_A: R5.2, TP105.1
H_ANT_B: TP106.1
H_AUX_IN: C36.1, R37.2, U6.2 (VIN)
H_BAT_SENSE: C28.1, R3.2, R4.1
H_BUTTON: C35.1, R40.2, R41.2, S1.2, S1.4
H_BUTTON_MCU: R41.1
H_D1_FREE: D1.2 (A)
H_LED_CTL_A: R30.1, TP1.1, U4.23 (RB2)
H_LED_CTL_B: R31.1, TP2.1, U4.22 (RB1)
H_PIR_SIG: Q2.3 (C), TP16.1
H_PIR_VDD: C37.1, J3.1, R33.2, U6.3 (VOUT), U106.2
H_RF_CONTROL: R6.2, R7.1
H_RF_VDD: C5.1, L1.2, Q8.2 (S)
H_RX_DETECT: C23.2, C40.1, R25.1
H_RX_ENABLE_CTL: R18.1, U4.12 (RC1)
H_RX_VDD: C17.1, C24.1, D3.2 (A), R20.2, R21.1, TP5.1, U3.8 (V+)
H_TUNE_1: R13.1, U4.17 (RC6)
H_TUNE_2: R14.1, U4.5 (RA3)
H_TUNE_3: R15.1, U4.6 (RA4)
H_TUNE_4: R16.1, U4.7 (RA5)
H_TUNE_5: R11.1, U4.11 (RC0)
ICSP_CLK: D4.1 (K), J1.1, R32.2, U4.27 (RB6/ICSPCLK)
ICSP_DAT: D5.1 (K), J1.2, R40.1, U4.28 (RB7/ICSPDAT)
MCLR_VPP: J1.3, U4.1 (RE3/~MCLR/VPP)
MOTOR_INA: U4.15 (RC4), U5.2 (INA)
MOTOR_INB: U4.16 (RC5), U5.3 (INB)
unnamed: C1.1, C101.1, L2.2, U1.1 (VIN), U1.3 (ON/OFF)
unnamed: C8.1, D1.1 (K), R6.1, U2.3
unnamed: C9.1, D1.3 (K), R7.2, U2.1
unnamed: C10.1, Q3.3 (C)
unnamed: C10.2, C11.2, C12.2
unnamed: C13.1, Q4.3 (C)
unnamed: C13.2, C14.2, C15.2
unnamed: C16.1, Q5.3 (C)
unnamed: C16.2, C29.2, C38.2
unnamed: C18.1, U3.5 (+)
unnamed: C18.2, R27.1, TP6.1
unnamed: C19.1, C20.2, R28.2, U3.3 (+)
unnamed: C21.1, C23.1, R24.1, U3.7
unnamed: C21.2, R23.1, R24.2, U3.6 (-)
unnamed: C22.1, R26.1, R27.2, U3.1
unnamed: C22.2, R26.2, R48.1, U3.2 (-)
unnamed: C25.1, U4.2 (RA0)
unnamed: C30.1, U4.9 (RA7), Y1.1
unnamed: C31.2, U4.10 (RA6), Y1.2
unnamed: C43.1, Q6.3 (C)
unnamed: C43.2, C44.2, C45.2
unnamed: C46.1, Q11.3 (C)
unnamed: C46.2, C47.2, C48.2
unnamed: D3.3 (K), R42.2
unnamed: J3.3, R33.1, R38.1
unnamed: J5.1, U5.8 (OUTA)
unnamed: J5.2, TP15.1, U5.5 (OUTB)
unnamed: LED1.1 (A1), R30.2
unnamed: LED1.2 (A2), R31.2
unnamed: Q1.1 (G), R44.2
unnamed: Q2.1 (B), R38.2, R39.1
unnamed: Q3.1 (B), R13.2
unnamed: Q4.1 (B), R14.2
unnamed: Q5.1 (B), R15.2
unnamed: Q6.1 (B), R16.2
unnamed: Q7.1 (B), R18.2, R19.1
unnamed: Q7.3 (C), R20.1
unnamed: Q8.1 (G), R9.2
unnamed: Q8.3 (G), R8.2
unnamed: Q8.4 (D), Q8.6 (D), R5.1
unnamed: Q11.1 (B), R11.2
unnamed: R8.1, U2.4
unnamed: R9.1, U2.6
unnamed: TP11.1, U4.14 (RC3)
PIC_RA1_RX_REF: R28.1, R29.1, TP7.1, U4.3 (RA1)
PIC_RB3_RETURN: R4.2, U4.24 (RB3)
PIC_RC7_TP17: TP17.1, U4.18 (RC7)
PIC_TP4_C41: C41.1, R42.1, R44.1, TP4.1, U4.25 (RB4)
R35_Q9: Q9.1, R35.2
RB5_OPT: R35.1, TP10.1, U4.26 (RB5)
RF_MONITOR_PAD: R10.1, TP3.1, U4.13 (RC2)
U1_ALT_PAD: C3.2, C4.2, R1.2, R2.2, U1.4 (NC)
VDD: C2.1, C3.1, C7.1, C32.1, C34.1, C102.1, J1.4, Q7.2 (E), R1.1, R19.2, R37.1, R39.2, TP103.1, U1.5 (VOUT), U2.5 (VCC), U4.20 (VDD), U5.1 (VCC)
VREF: C39.1, R21.2, R22.2, R23.2, R48.2, TP104.1, U4.4 (RA2), U4.21 (RB0)
VSYS: C27.1, C33.1, L1.1, L2.1, Q1.2 (S), R3.1, U5.4 (VDD)

Notes on the sheet:
01 POWER / INPUT FILTER
H01: likely S-1200B45 LDO. Nominal 4.5 V is a candidate, not a measured rail.
U1 datasheet symbol: S-1200B45 SOT-23-5. Pin 4 is internally open; option pads retained.
Empty options: R1/C3 free ends join regulated VDD; R2/C4 free ends join GND.
02 PIC CONTROLLER / CLOCK / ICSP
User: RA3/R14, RA4/R15, RA5/R16, RC0/R11, RC6/R13. RC2 -> TP3; RB0 -> VREF. RC1 -> R18 via V053-V070.
R3/R4 sensing candidate; R4 returns to RB3. C28 value estimated.
03 MOTOR / BUTTON / BATTERY INTERFACE
User: PIC15/RC4 -> INA pin2; PIC16/RC5 -> INB pin3. Motor output polarity remains inferred.
C27: motor-supply bypass; value unmeasured.
Q1: R1A -> FMOS3401A PMOS candidate. Battery+ at D3; post-Q1 supply at S2; G1 via R44.
H06: S1 pairs and RC debounce inferred.
04 ANTENNA EXCITATION / LOGIC / INDICATOR
H07: C14R inverter candidate. Q8 source rail inferred; C6 destination unresolved.
H09: 3724A matches SIL3724A N/P MOSFET pair. Both units share one package.
V113/V115: Q8 centre pin5 GND. V114 is U2 pin2 GND, not Q8 pin2.
05 RF RECEIVE / GAIN / ENVELOPE
H10-H12: working topology around photographed 120k feedback resistors. Filters, bias, and interstage routes inferred.
C42 / R47 / R46: DNP options, exact pads unresolved.
06 SWITCHED ANTENNA CAPACITANCE
H13: 2H devices are probably PNP BJTs (MMBTA55 family; PBSS5140T is an alternative). Capacitor values unknown.
v0.9: user-reviewed GND returns replace previous antenna rails on this capacitor bank.
Local three-capacitor junctions retained. Hidden links from these midpoints to antenna remain unknown.
Do not infer complete tuning topology from local connections. Transistor identity/orientation remains provisional.
07 PIR / AUXILIARY RAIL
H14-H15: C2N supports S-812C33AMC 3.3V LDO. C/R3 ground supported by resistance.
08 UNRESOLVED / UNPOPULATED OPTIONS
D4/D5 opposite vias join rear GND copper. D6 type and routes remain uncertain.
READING THIS WORKING RECONSTRUCTION
One sheet. Functional wiring is proposed; this is not a verified production circuit.
150 original main-board catalog entries, including DNP footprints and named pads.
H_* = inferred inter-block net. Other net names do not imply measurement.
? on a part value or pin function means an estimate or candidate identity.
Library pin numbers are mapped to photo pads in evidence/pin_crosswalk.json.
U2 and U3 use multiple symbol units on this same sheet, including supply units.
28 original local photo fragments retained; Q1.L-R43.2 withdrawn by user.
PIC GPIOs are intentionally unassigned where photographs cannot support a map.
DNP = unpopulated. An open pin means unresolved, not a certified no-connect.
PIR daughterboard internals are not yet traced; J3 represents its interface.
No capacitor value or rail voltage in this drawing was electrically measured.
See docs/RECONSTRUCTION.md for evidence, alternatives, and calculations.
Spare footprints / unassigned test pads
v0.9.9 | KiCad 10.0.5 | 2026-10-08
BATTERY+ -> Q1 -> VSYS / U5 pin4. Board VDD / TP103 = VDD -> U5 pin1.
VDD / TP103: regulated logic supply VDD; candidate 4.5V, not measured. V082 confirmed here.
V082 -> VDD / TP103. D3 terminal unresolved; existing H_RX_VDD branch remains inferred.
D2: 4P unidentified; old BAV99 clamp ties withdrawn.
User: V072 = TP6, not R22.2. V079/V080 = U3 pin5; separate from TP6 across C18.
U3 alternative: MCP6002-I/SN; same pin roles, electrical suitability to verify.
U5 alternative: DRV8212PDSGR. Different package/pins; redesign required.
U6: 3.3V is the candidate rating, not a voltage measurement. NC4/5 board ties unresolved.
C6: F-P 10 ohm, F-G 300 kohm suggests a supply-related node; exact path unresolved.
User: V063-V064 confirms R37/R39 feed on regulated VDD.
Q7: 11.2 kohm V064-V070 fits R18+R19. Supply-switch topology inferred; RC1 drives R18 via V053-V070.
