kerby2000/PetSafe-PCB/tools/reconcile_via_review.py

"""Overlay the user's current review without changing stable site IDs.

`net` is the reviewed site assignment; `modeled_nets` is descriptive only and
may contain an older unverified hypothesis. Neither expands to the whole net.
"""
from pathlib import Path
from collections import defaultdict, Counter
import json,csv
R=Path(__file__).resolve().parents[1]
def apply(out):
    review=json.loads((R/'evidence/via_user_review.json').read_text())
    model=json.loads((R/'evidence/reconstruction.json').read_text())
    by=defaultdict(list)
    for r in review['reports']:by[r['id']].append(r)
    original_ids=set(by)
    for correction in review.get('followup_corrections',[]):
        for r in correction['assignments']:by[r['id']]=[r]
    current_ids=set(by)
    membership={e:n['net'] for n in model['nets'] for e in n['endpoints']}
    sites={s['id']:s for s in out['sites']}
    conflicts={}
    rejected=['V033','V050','V117','V120','V121','V122','V124']
    def annotate(ids,ends,note,net=None):
        for i in ids:
            s=sites[f'V{i:03d}'];s['endpoints']=ends;s['component_crosscheck']=note
            if net:s['net']=net
    for s in out['sites']:
        s.pop('conflict',None)
        s['net']={'H_GND':'GND','H_VDD':'VDD','H_VBAT':'VSYS','H_BAT_DETECT':'BATTERY+','PIC_RB0_VREF':'VREF'}.get(s.get('net'),s.get('net'))
        s.update(active=s['id'] not in rejected,user_reports=by[s['id']],review_status='USER_REPORTED' if by[s['id']] else 'NOT_IN_USER_LIST')
        kinds={r['kind'] for r in by[s['id']]}
        if 'ground' in kinds:s['net']='GND';s['confidence']='User GND report; no per-site ohms supplied'
        if any('MX512' in r['claim'] or (r['kind']=='motor_supply') for r in by[s['id']]):
            s['net']='VSYS';s['confidence']='User common-net report to MX512H pin4; no per-site ohms supplied'
        if s['id'] in conflicts:
            s['review_status']='CONFLICT';s['conflict']=conflicts[s['id']]
            if s['id']!='V025':s['net']=None
        if not s['active']:
            s.update(review_status='REJECTED_NOT_VIA',net=None,endpoints=[],note=f"User rejects {s['id']} as a recognition error. ID retained as a tombstone; excluded from active markers.")
    annotate([1,2],['U5.4'],'MX512H motor VDD, distinct from logic VCC pin1.','VSYS')
    annotate([3,4],['C27.1'],'C27 left photo pad on user motor-supply island.','VSYS')
    annotate([8,9,10],['C27.2'],'C27 right photo pad on user GND island.','GND')
    annotate([6],['C33.2'],'User adds C33 to earlier GND report; pad2 selected from photo/model.','GND')
    annotate([7],['C34.2'],'User adds C34 to earlier GND report; pad2 selected from photo/model.','GND')
    for i in [11,12,13,14]:
        sites[f'V{i:03d}'].update(net='VSYS',endpoints=['Q1.L'],excluded_endpoints=['R43.2'],reported_supply='MX512H pin4 VDD / motor supply VSYS',confidence='User confirms post-Q1 motor rail; candidate PMOS function from R1A datasheet and photo',component_crosscheck='User explicitly confirms same rail as MX512H pin4. Q1.L reaches motor VSYS, distinct from regulated VDD/TP103. R43.2 remains excluded.')
    sites['V015'].update(endpoints=['R43.2','TP14.1'],net='BATTERY+',excluded_endpoints=['Q1.L'],component_crosscheck='User confirms V015-TP14 and R43.2. IMG_2438 places TP14 on battery-positive copper to Q1 single pad3. Raw battery stays separate from post-Q1 motor VDD; the former battery-detect net name is withdrawn.')
    annotate([16,22],['U5.2','U4.15'],'User confirms V016-V022 joins U5 INA pin2 to PIC15 RC4.','MOTOR_INA')
    annotate([19,23],['U5.3','U4.16'],'User confirms V019-V023 joins U5 INB pin3 to PIC16 RC5.','MOTOR_INB')
    for i in [16,22]:sites[f'V{i:03d}']['joined_vias']=['V016','V022']
    for i in [19,23]:sites[f'V{i:03d}']['joined_vias']=['V019','V023']
    annotate([17],['R42.1','R44.1','TP4.1','U4.25'],'User confirms V017-TP4, previously mapped to PIC25/RB4. R42.1 explicitly named; R44 free pad1 photo-selected. Old ANT2 hypothesis remains withdrawn.','PIC_TP4_C41')
    annotate([18],['C35.2'],'User adds C35 to earlier GND report; pad2 selected from photo/model.','GND')
    annotate([20],['R40.1'],'User identifies R40; photo selects upper/free pad1 on the existing ICSP DAT node.','ICSP_DAT')
    annotate([21],['Q9.R'],'Q9 DNP lower-right pad; stock pin2.','GND')
    annotate([24],['R32.1'],'R32 upper photo pad. Old PIR assignment withdrawn.','GND')
    annotate([26],['U4.21','VREF.1'],'User V026-VREF report with prior V026-PIC21/RB0 mapping. VREF is native TP104; voltage/function not established.','VREF')
    annotate([29],['C25.2','C26.2'],'User adds both capacitors to earlier GND report; return pads selected from photos/model. C26.1 remains unresolved.','GND')
    annotate([31],['U4.2','C25.1'],'User RA0/C25 association corroborates existing local signal node.','PIC_RA0_FILTER')
    annotate([35],['U4.4','C39.1','VREF.1'],'User confirms V035-VREF TP; earlier local PIC4/RA2-C39.1 photo route retained. Same VREF node as V026/RB0 and V071/R21.2.','VREF')
    sites['V035']['confidence']='User V035-VREF continuity; PIC4/C39 pad association from earlier photo trace'
    annotate([42],['U4.20','C32.1','VDD.1'],'User confirms V042-board VDD TP, matching prior PIC20/C32.1 photo mapping. Regulated VDD, not motor VDD or raw battery.','VDD')
    sites['V042']['confidence']='User continuity to board VDD; PIC20/C32.1 local association from photo'
    annotate([34],['R3.1'],'User VDD/R3, previously explicitly the same net as V001 and MX512H pin4. This is motor supply VSYS, not regulated VDD.','VSYS')
    annotate([40],['C28.2'],'User adds C28 to earlier GND report; return pad selected from photo/model.','GND')
    for i,p in [(36,5),(37,6),(39,7),(47,11),(49,13)]:
        s=sites[f'V{i:03d}'];s.pop('candidate_endpoints',None)
        s.update(endpoints=[f'U4.{p}'],net=None,confidence='User-confirmed PIC pin-to-via association; no new per-site ohms supplied',component_crosscheck='User confirms this PIC pin-to-via connection. Earlier under-body alignment hypothesis superseded. Onward destination remains unknown; not NC. Front marker coordinates remain projected.')
    annotate([49],['U4.13','TP3.1'],'User confirms V049 reaches TP03 (board TP3), with earlier PIC13/RC2 association. Existing TP3-R10.1 local branch remains photo-derived; no new resistance supplied.','RF_MONITOR_PAD')
    sites['V049']['confidence']='User endpoint association; no numerical resistance for TP3 route'
    sites['V053'].pop('pending_endpoints',None)
    annotate([57,58],['R2.1','C4.1'],'DNP option free pads in the front ground copper.','GND')
    annotate([59,61],['L2.1'],'User adds L2 to the earlier common motor-supply report; source/right pad1 selected from photo/model.','VSYS')
    annotate([60],['Q2.L'],'User adds Q2 to earlier GND report; local ground-side pad selected from photo/model.','GND')
    annotate([63],['R37.1','R39.2'],'User V064-V063 confirms R37/R39 feed on regulated board VDD. Motor supply remains separate.','VDD')
    annotate([64],['R1.1','C3.1','VDD.1','U1.R1'],'Regulated board VDD island. Do not equate this use of VDD with MX512H motor pin4.','VDD')
    annotate([65],['C2.2'],'User adds C2 to earlier GND report; return pad selected from photo/model.','GND')
    annotate([68],['C37.2','C36.2'],'User adds both capacitors to earlier GND report; return pads selected from photos/model.','GND')
    annotate([67],['U6A.R1','J3.1'],'User confirms V067-J3 pin1/red wire; retain earlier local U6A.R1 pad association. Other H_PIR_VDD branches remain qualified.','H_PIR_VDD')
    annotate([70],['R18.1'],'User V064-V070 = 11.2 kohm excludes direct VDD. Nominal R18 1.2k + R19 10k fits the measured path; base-input topology supported by photo/circuit inference. Onward control source unknown.','H_RX_ENABLE_CTL')
    annotate([53,70],['U4.12','R18.1'],'User confirms V053-V070 and excludes V053-VREF. PIC12/RC1 reaches R18 input; Q7 local operating role remains inferred. No numeric ohms supplied.','H_RX_ENABLE_CTL')
    for i in [53,70]:sites[f'V{i:03d}'].update(joined_vias=['V053','V070'],confidence='User continuity report; no numerical resistance supplied')
    annotate([71],['R21.2','VREF.1','U4.21'],'User confirms V071-VREF, previously mapped to PIC21/RB0 via V026. Other receiver-bias branches remain photo/circuit hypotheses.','VREF')
    for i in [26,71]:sites[f'V{i:03d}']['joined_vias']=['V026','V071']
    sites['V072'].update(net='RX_A_FILTER',endpoints=['TP6.1'],excluded_endpoints=['R22.2'],confidence='User identifies TP6 and explicitly excludes R22.2',component_crosscheck='User identifies TP6. Existing C18.2/R27.1 branches on RX_A_FILTER remain hypotheses; the via report does not certify the whole modeled net. TP6 remains separate from U3.5 across C18.')
    sites['V073'].update(net='GND',endpoints=[],component_crosscheck='User correction: GND only. R19 association removed; no R19 ground merge. V075 is now user-associated with Q7; its exact terminal is unresolved.')
    sites['V075'].update(net='VDD',endpoints=['Q7.R','R19.2'],component_refs=['Q7','R19'],candidate_endpoints=[],confidence='Rail measured via V064; local terminals selected from IMG_2434 and 11.2 kohm R18+R19 path, not separate pad measurements.',component_crosscheck='V064-V075 confirms regulated VDD. IMG_2434 shows the R19/Q7 paired-pad continuation; V064-V070 11.2 kohm supports R18+R19 base-input/pull-up arrangement. Q7.R/native2 and R19.2 now modeled on VDD as a supported reconstruction, not user-probed exact terminal proof.')
    annotate([76],['R22.1'],'R22 opposite/right photo pad; user GND corroborates return.','GND')
    annotate([77],['C19.2','R29.2'],'User explicitly confirms the C19-R29 junction is GND. R29 opposite the PIC3/TP7 end is pad2; C19 pad2 is assigned to the upper photo pad beside the via. Earlier C19-to-clamp and R29-to-U3.5 guesses withdrawn.','GND')
    annotate([78],['C17.2'],'User adds C17 to earlier GND report; return pad selected from existing photo/model.','GND')
    annotate([79,80],['U3.5'],'User identifies SGM8542 pin5 for both vias. Existing original C18.1 local fragment retained on RX_B_PLUS; TP6 lies on the opposite side of C18 and is not merged.','RX_B_PLUS')
    for i in [79,80]:sites[f'V{i:03d}']['confidence']='User explicit U3 pin5 association; no new per-site ohms supplied'
    annotate([82],['VDD.1'],'User confirms V082-board VDD test point (native TP103), regulated logic VDD. D3 exact terminal unconfirmed; no H_RX_VDD merge implied.','VDD')
    sites['V082']['confidence']='User continuity report to TP103; D3 terminal unresolved'
    sites['V082']['component_refs']=['D3']
    annotate([83],['C40.2'],'User adds C40 to earlier GND report; return pad selected from existing photo/model.','GND')
    for i,r,n in [(91,'R11',5),(97,'R16',4),(102,'R15',3),(108,'R14',2)]:
        annotate([i],[r+'.1'],'User identifies resistor; free upper photo pad1 selected. Tuning control role remains a hypothesis and onward GPIO is not identified.',f'H_TUNE_{n}')
    for i,q in [(89,'Q11'),(94,'Q6'),(99,'Q5'),(104,'Q4')]:
        annotate([i],[q+'.L'],'Photo left transistor pad to user GND via; assumed emitter role not confirmed.','GND')
    annotate([87,88],[c+'.1' for c in ['C47','C44','C29','C14','C11']],'Shared lower front-capacitor band; old antenna rail assumption withdrawn.','GND')
    for i,c in [(93,'C48'),(96,'C45'),(101,'C38'),(105,'C15')]:
        annotate([i],[c+'.1'],'Rear capacitor ground-side land; other pad joins local tuning midpoint.','GND')
    for i,n,cs in [(90,5,['C46','C47','C48']),(95,4,['C43','C44','C45']),(100,3,['C16','C29','C38']),(103,2,['C13','C14','C15']),(107,1,['C10','C11','C12'])]:
        annotate([i],[c+'.2' for c in cs],'User front-pair junction plus rear-land photo pairing; onward hidden connection to antenna remains unknown.',f'TUNE_{n}_MID')
    annotate([112],['C8.2'],'User adds C8 to earlier GND report; lower photo return pad selected.','GND')
    annotate([113,115],['Q8.B2'],'User corrects island destination to the centre pad: B2/package pin5, already modeled as GND. Previous B1/B3 annotation was wrong. Independent earlier D-E low-resistance evidence for the outer-pad join is retained.','GND')
    for i in [113,115]:
        sites[f'V{i:03d}'].update(excluded_endpoints=['Q8.B1','Q8.B3'],confidence='User centre-pad/GND clarification; corroborates earlier S-G low resistance')
    annotate([114],['U2.T2'],'User corrects the component to U2.T2, native pin2, not Q8.T2. Earlier GND report retained; confirms existing U2 ground. No evidence for the Q8 supply rail.','GND')
    sites['V114'].update(excluded_endpoints=['Q8.T2'],confidence='User U2.T2 correction plus earlier GND report; consistent with existing U2 pin2 ground')
    annotate([116],['R10.2'],'R10 free end; no longer singleton monitor hypothesis.','GND')
    annotate([118],['C7.2'],'User adds C7 to earlier GND report; lower photo return pad selected.','GND')
    annotate([119],['C9.2'],'User identifies C9; photo selects lower pad2. GND is retained as the existing photo/model inference, not a new user ground measurement.','GND')
    sites['V119']['confidence']='User component association; pad and GND inferred from photo/model'
    annotate([125,126],['C5.2'],'User identifies C5 negative terminal and earlier GND; native capacitor pad2 already grounded.','GND')
    annotate([127],['LED1.BL','LED1.BR'],'User GND/LED1 report. IMG_2432 common pair opposite resistor-fed pads selected as existing BL/BR (stock3/4); physical/internal LED mapping remains provisional.','GND')
    sites['V127']['confidence']='User GND/component report; common pair selected from photograph and existing model'
    for va,vb,pin,res,n in [(36,108,5,'R14',2),(37,102,6,'R15',3),(39,97,7,'R16',4),(47,91,11,'R11',5)]:
        annotate([va,vb],[f'U4.{pin}',res+'.1'],f'User working via pair V{va:03d}-V{vb:03d}; PIC control to resistor confirmed. No numerical ohms supplied.',f'H_TUNE_{n}')
        for i in [va,vb]:sites[f'V{i:03d}'].update(joined_vias=[f'V{va:03d}',f'V{vb:03d}'],confidence='User continuity report; exact resistance not supplied')
    for i in [63,64,75]:sites[f'V{i:03d}']['joined_vias']=['V063','V064','V075']
    sites['V053']['excluded_vias']=['V071','V026'];sites['V071']['excluded_vias']=['V053'];sites['V026']['excluded_vias']=['V053']
    sites['V053']['excluded_endpoints']=['VREF.1']
    sites['V090']['excluded_vias']=['V095','V100','V103','V107']
    for i in [95,100,103,107]:sites[f'V{i:03d}']['excluded_vias']=['V090']
    for i in [100,103,107]:
        sites['V095']['excluded_vias'].append(f'V{i:03d}')
        sites[f'V{i:03d}']['excluded_vias'].append('V095')
    sites['V064']['excluded_vias']=['V070'];sites['V070']['excluded_vias']=['V064']
    for i in [64,70]:sites[f'V{i:03d}']['resistive_measurements']=[dict(vias=['V064','V070'],reading='11.2 kohm',resistance_ohms=11200,reverse_reading=None)]
    sites['V049']['excluded_vias']=['V071'];sites['V071']['excluded_vias'].append('V049')
    for i in [49,71]:sites[f'V{i:03d}']['resistive_measurements']=[dict(vias=['V049','V071'],reading='20 kohm',resistance_ohms=20000,reverse_reading=None)]
    variable=json.loads((R/'evidence/via_pair_followup_20261008_rc2.json').read_text())['inconclusive_pairs'][0]
    for i,other in [(49,'V070'),(70,'V049')]:
        sites[f'V{i:03d}']['inconclusive_vias']=[other]
        sites[f'V{i:03d}']['resistive_measurements'].append(variable)
    for s in out['sites']:
        s['modeled_nets']=sorted({membership[e] for e in s['endpoints'] if e in membership})
        if not s['active']:
            s.update(review_status='REJECTED_NOT_VIA',net=None,endpoints=[],modeled_nets=[],component_crosscheck='User rejects this detection as not a via. Stable ID retained; excluded from active markers.')
        elif s['user_reports'] and s['net'] and s['review_status']!='CONFLICT':s['review_status']='ASSIGNED'
        elif not s['user_reports'] and s['net']:s['review_status']='PHOTO_LOCAL'
    out.update(revision='v0.9.9',review_update_id='battery-q1-post-q1-supply-separated',user_review_source='evidence/via_user_review.json',
        user_review_method=review['method'],supply_naming=review['supply_naming'],
        review_summary=dict(catalogued_ids=len(sites),active_sites=sum(s['active'] for s in sites.values()),user_reported_ids=len(current_ids),original_user_reported_ids=len(original_ids),
            omitted_from_user_list=sorted(set(sites)-current_ids),rejected=rejected,conflicts=list(conflicts),
            statuses=dict(Counter(s['review_status'] for s in sites.values()))),
        new_model_connections=json.loads((R/'evidence/v099_net_changes.json').read_text())['changes'])
    return out

if __name__=='__main__':
    p=R/'evidence/via_audit.json';out=apply(json.loads(p.read_text()))
    p.write_text(json.dumps(out,indent=2)+'\n',encoding='utf-8')
    fields=['id','active','rear_x','rear_y','front_x','front_y','rear_appearance','front_match','review_status','user_claims','endpoints','net','modeled_nets','component_crosscheck','conflict']
    with (R/'evidence/via_inventory.csv').open('w',newline='',encoding='utf-8') as f:
        w=csv.DictWriter(f,fieldnames=fields);w.writeheader()
        for s in out['sites']:
            w.writerow(dict(id=s['id'],active=s['active'],rear_x=s['rear_xy'][0],rear_y=s['rear_xy'][1],front_x=s['front_xy'][0],front_y=s['front_xy'][1],
                rear_appearance=s['rear_appearance'],front_match=s['front_match'],review_status=s['review_status'],user_claims='; '.join(r['claim'] for r in s['user_reports']),
                endpoints=';'.join(s['endpoints']),net=s['net'] or '',modeled_nets=';'.join(s['modeled_nets']),component_crosscheck=s.get('component_crosscheck',''),conflict=s.get('conflict','')))
    print(out['review_summary'])
