kerby2000/PetSafe-PCB/tools/validate_native.py

"""Compare the authored electrical model with a native KiCad XML netlist."""
from pathlib import Path
from collections import Counter
import json, hashlib, xml.etree.ElementTree as ET
ROOT=Path(__file__).resolve().parents[1]
def sha(p):return hashlib.sha256(p.read_bytes()).hexdigest()
def main():
    m=json.loads((ROOT/'evidence/reconstruction.json').read_text())
    native=ET.parse(ROOT/'output/PetSafe_netlist.xml')
    def translated(ep):
        if 'native_pin_crosswalk' in m:return m['native_pin_crosswalk'][ep]
        r,p=ep.rsplit('.',1)
        return m['reference_map'].get(r,r)+'.'+p
    actual={frozenset(n.attrib['ref']+'.'+n.attrib['pin'] for n in net.findall('node')):net.attrib['name'] for net in native.findall('./nets/net')}
    expected={frozenset(map(translated,n['endpoints'])):n['net'] for n in m['nets']}
    differences=[dict(net=n,pins=sorted(p)) for p,n in expected.items() if p not in actual]
    extras=[dict(net=n,pins=sorted(p)) for p,n in actual.items() if len(p)>1 and p not in expected]
    assert not differences and not extras,(differences,extras)
    assert len(native.findall('./components/comp'))==150
    assert len(native.findall('./design/sheet'))==1
    old=json.loads((ROOT/'reference/v01/evidence/reconstruction.json').read_text())
    withdrawn={f['net']:f for f in m.get('withdrawn_original_fragments',[])}
    assert set(withdrawn)=={'V_Q1_LEFT'}, 'Only the explicitly user-refuted original fragment may be skipped'
    assert withdrawn['V_Q1_LEFT']['user_authorization']=='Remove Q1.L–R43.2 connection'
    for net in old['nets']:
        ep=set(map(translated,net['endpoints']))
        if net['net'] in withdrawn:
            assert set(net['endpoints'])==set(withdrawn[net['net']]['endpoints'])
            assert not any(ep<=pins for pins in actual), 'Withdrawn Q1/R43 tie revived'
            continue
        assert any(ep<=pins for pins in actual),net
    manifest=json.loads((ROOT/'evidence/original_photo_manifest.json').read_text())
    for p in manifest:
        source=ROOT/'photos/originals'/p['file']
        assert sha(source)==p['sha256'] and source.stat().st_size==p['bytes'],p
    erc=json.loads((ROOT/'output/erc.json').read_text())
    violations=[v for sheet in erc['sheets'] for v in sheet['violations']]
    counts=Counter(v['type'] for v in violations)
    unexpected=set(counts)-{'pin_not_connected','isolated_pin_label','power_pin_not_driven','pin_not_driven'}
    assert not unexpected,counts
    sch=ROOT/'schematic/PetSafe_1001339.kicad_sch'
    assert '(no_connect ' not in sch.read_text()
    assert '(lib_id "PetSafe_Working:' not in sch.read_text()
    definitions={(p.attrib['lib'],p.attrib['part']) for p in native.findall('./libparts/libpart')}
    custom=sum(lib=='PetSafe_Datasheet' for lib,part in definitions)
    assert custom==4 and len(definitions)==24,definitions
    # Independent manufacturer pin-table contracts, checked in native KiCad output.
    contracts={
        'U1':('S-1200B45-M5T1','Package_TO_SOT_SMD:SOT-23-5',
              [('VIN','power_in'),('VSS','power_in'),('ON/OFF','input'),('NC','passive'),('VOUT','power_out')]),
        'U5':('MX512H','Package_SO:SOIC-8_3.9x4.9mm_P1.27mm',
              [('VCC','power_in'),('INA','input'),('INB','input'),('VDD','power_in'),('OUTB','tri_state'),('GND','power_in'),('GND','power_in'),('OUTA','tri_state')]),
        'U6':('S-812C33AMC','Package_TO_SOT_SMD:SOT-23-5',
              [('VSS','power_in'),('VIN','power_in'),('VOUT','power_out'),('NC','passive'),('NC','passive')]),
        'Q8':('SIL3724A','Package_TO_SOT_SMD:SOT-23-6',
              [('G','input'),('S','passive'),('G','input'),('D','passive'),('S','passive'),('D','passive')])}
    for ref,(part,footprint,pins) in contracts.items():
        lib=native.find(f'./libparts/libpart[@lib="PetSafe_Datasheet"][@part="{part}"]')
        actual_pins={p.attrib['num']:(p.attrib['name'],p.attrib['type']) for p in lib.findall('./pins/pin')}
        assert actual_pins=={str(i):p for i,p in enumerate(pins,1)},(ref,actual_pins)
        comp=native.find(f'./components/comp[@ref="{ref}"]')
        assert comp.findtext('footprint')==footprint
        assert comp.findtext('datasheet')==lib.findtext('docs')
        assert comp.findtext('description')==lib.findtext('description')
    report=dict(date='2026-10-08',native_tool=native.findtext('./design/tool'),native_load_and_export='PASS',single_sheet='PASS',catalog_components=150,symbol_units=155,physical_pins=352,stock_library_symbols=len(definitions)-custom,custom_symbols=custom,proposed_net_partitions=len(expected),netlist_partition_comparison='PASS',unintended_multi_pin_nets=0,retained_original_visual_fragments=len(old['nets'])-len(withdrawn),withdrawn_original_visual_fragments=sorted(withdrawn),original_photo_checksums=f'PASS ({len(manifest)} files)',unresolved_physical_pins=len(m['unresolved_pins']),erc_total=len(violations),erc_by_type=dict(counts),erc_status='OPEN FINDINGS - candidate IC pin types checked; unknown board routing remains',gui_open='NOT_TESTED (native CLI validated)',hardware_verification='PARTIAL: recorded U6/Q8 resistance and selected PIC meter/visual routes; user via reports plus photo cross-checks; circuit hypotheses remain; no functional or voltage test',physical_pcb_layout='NOT_CREATED',schematic_sha256=sha(sch),input_zip_sha256=sha(ROOT/'input/PetSafe_KiCad_RE_v01.zip'))
    report['datasheet_symbol_pin_contracts']='PASS (U1: 5 pins; U5: 8 pins; U6: 5 pins; Q8: 6 pins; types, footprints and source properties)'
    (ROOT/'evidence/validation.json').write_text(json.dumps(report,indent=2),encoding='utf-8',newline='\n')
    (ROOT/'evidence/validation_log.txt').write_text('Native KiCad model/netlist cross-check: PASS\n'+json.dumps(report,indent=2)+'\n',encoding='utf-8',newline='\n')
    print(json.dumps(report,indent=2))
if __name__=='__main__':main()
